dallaszkorben/diy-greenwall/3D/STL/lamp.hanger/lamp.hanger_console_extention.3mf

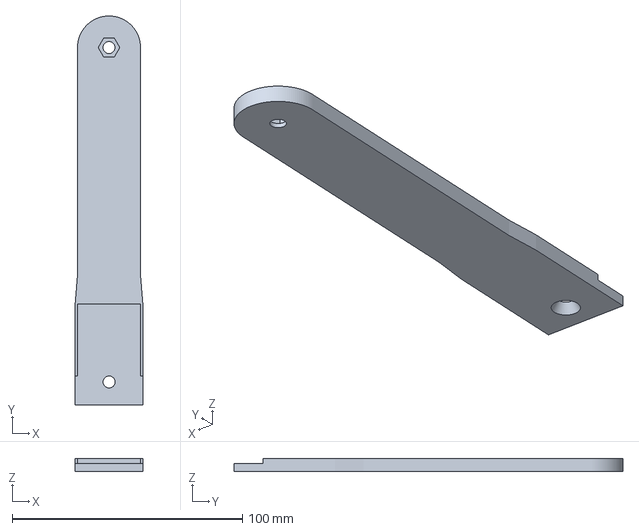
[picture p31: CAD file, 2024-04-21]
3D/STL/lamp.hanger/lamp.hanger_console_extention.3mf
29.4 x 169.0 x 5.50 mm
