dallaszkorben/diy-greenwall/3D/STL/pipe/spillway.reducer.FCStd

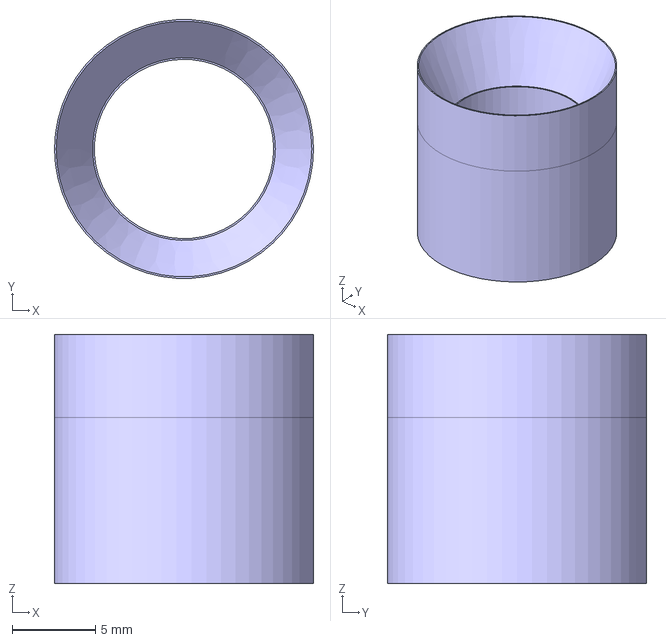
[picture p32: CAD file, 2022-04-12]
3D/STL/pipe/spillway.reducer.FCStd
15.6 x 15.6 x 15.0 mm
