dallaszkorben/diy-greenwall/3D/STL/round.container.hanger/Round.Container.Hanger.118mm.3mf

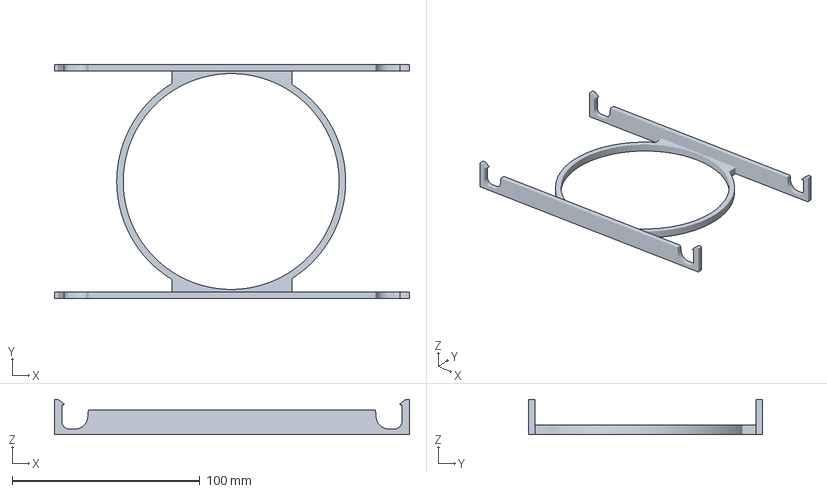
[picture p33: CAD file, 2024-04-21]
3D/STL/round.container.hanger/Round.Container.Hanger.118mm.3mf
189.2 x 124.9 x 18.7 mm
