dallaszkorben/diy-greenwall/3D/STL/sonic.sensor.cap.stl

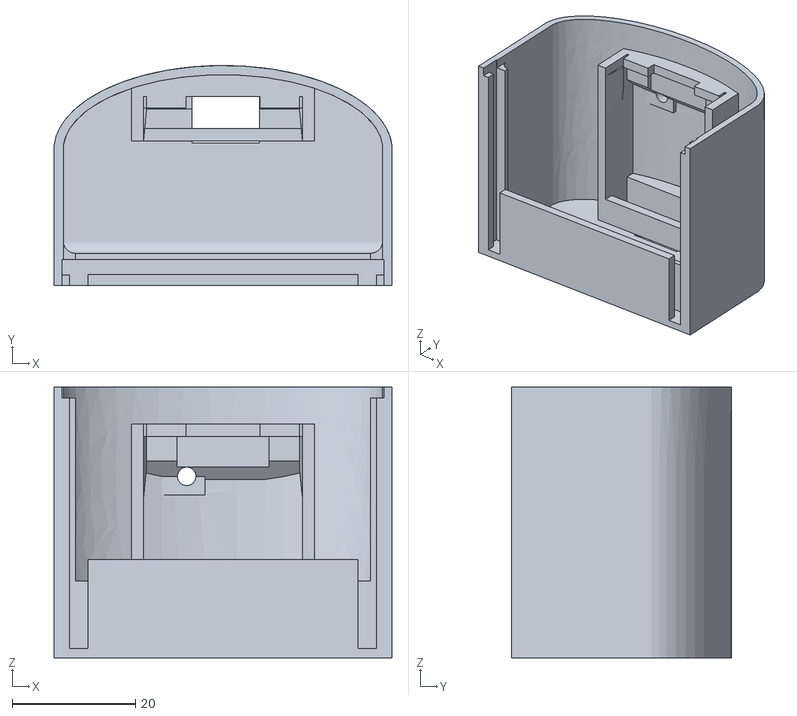
[picture p34: CAD file, 2021-12-05]
3D/STL/sonic.sensor.cap.stl
54.9 x 35.7 x 44.0
