dallaszkorben/diy-greenwall/3D/STL/station.lamp.pump/station.lamp.pump.100w.C8.stl

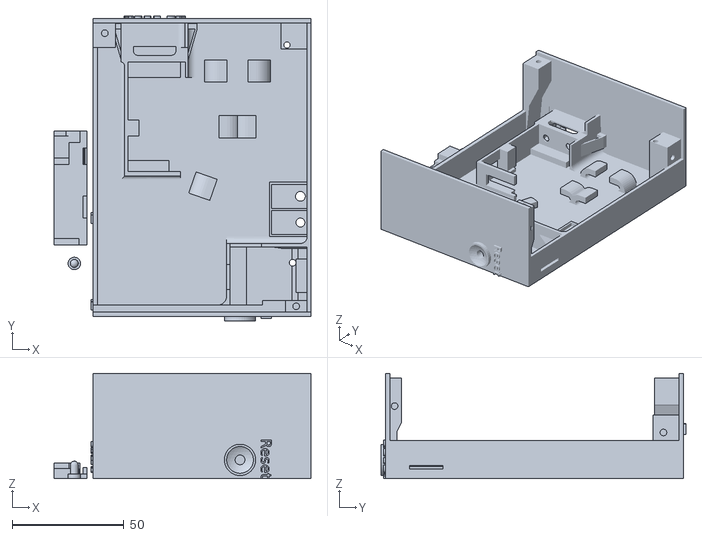
[picture p35: CAD file, 2022-08-27]
3D/STL/station.lamp.pump/station.lamp.pump.100w.C8.stl
114.9 x 136.2 x 47.0
