dallaszkorben/diy-greenwall/3D/STL/station.lamp/station.lamp.1X42v.stl

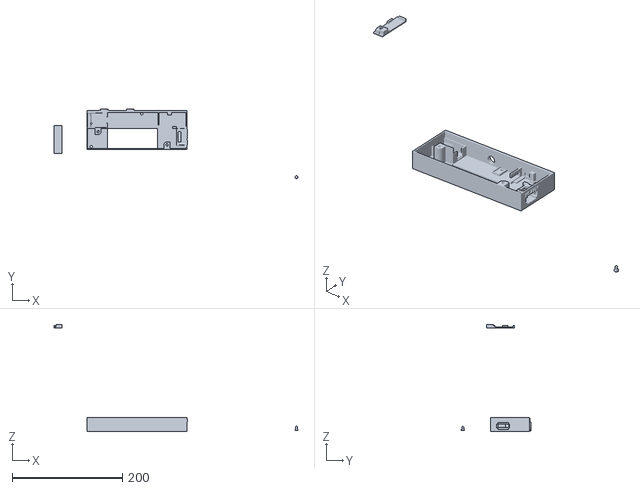
[picture p36: CAD file, 2024-08-11]
3D/STL/station.lamp/station.lamp.1X42v.stl
442.3 x 126.0 x 194.5
