dallaszkorben/diy-greenwall/3D/STL/station.pump/station.pump.1X12v-Frame.stl

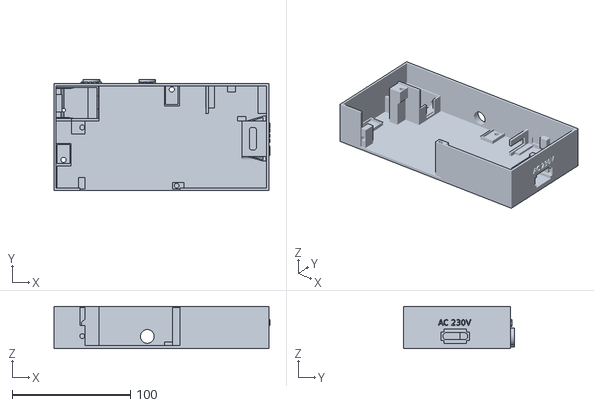
[picture p37: CAD file, 2024-08-11]
3D/STL/station.pump/station.pump.1X12v-Frame.stl
182.8 x 94.0 x 35.7
