dallaszkorben/diy-greenwall/3D/STL/station.sensor/station.sensor.console.stl

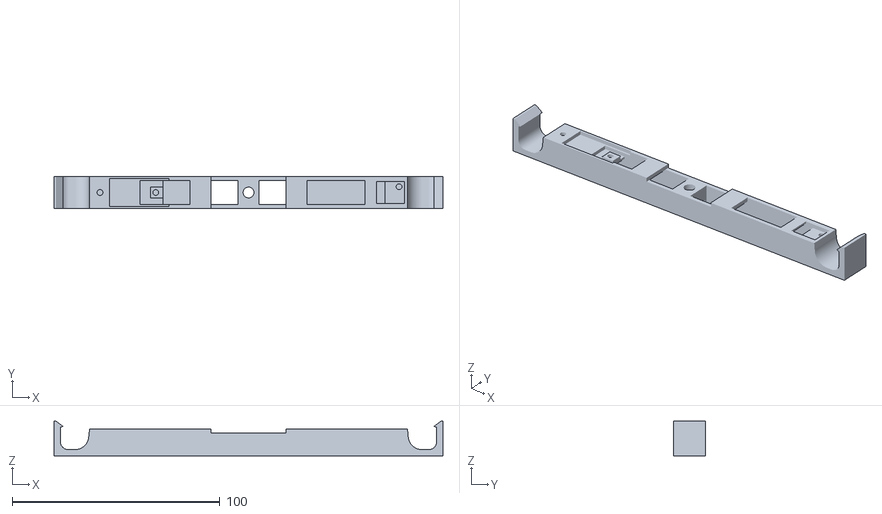
[picture p38: CAD file, 2022-10-24]
3D/STL/station.sensor/station.sensor.console.stl
187.2 x 15.6 x 16.7
