dallaszkorben/diy-greenwall/3D/STL/tmp/capacitor.FCStd

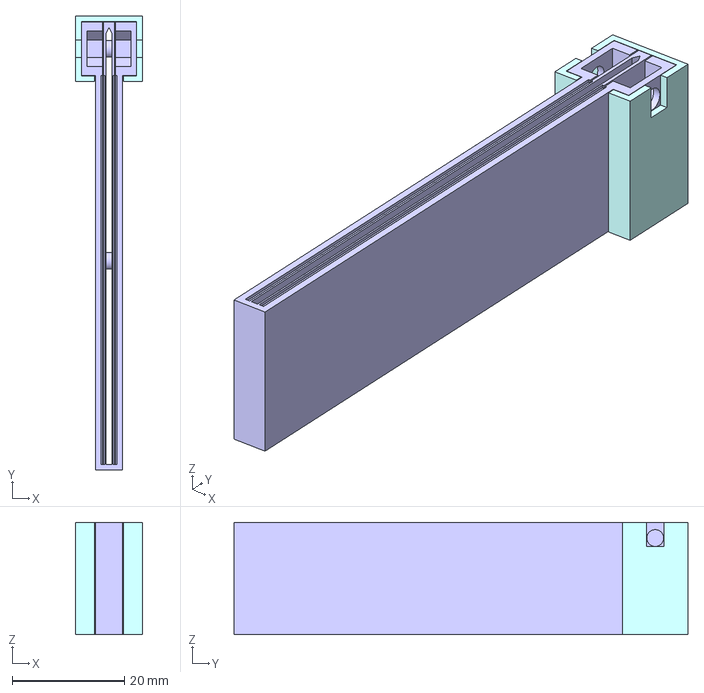
[picture p39: CAD file, 2023-01-22]
3D/STL/tmp/capacitor.FCStd
11.9 x 81.1 x 20.0 mm
