dallaszkorben/diy-greenwall/3D/STL/watertank/watertank_clamp.stl

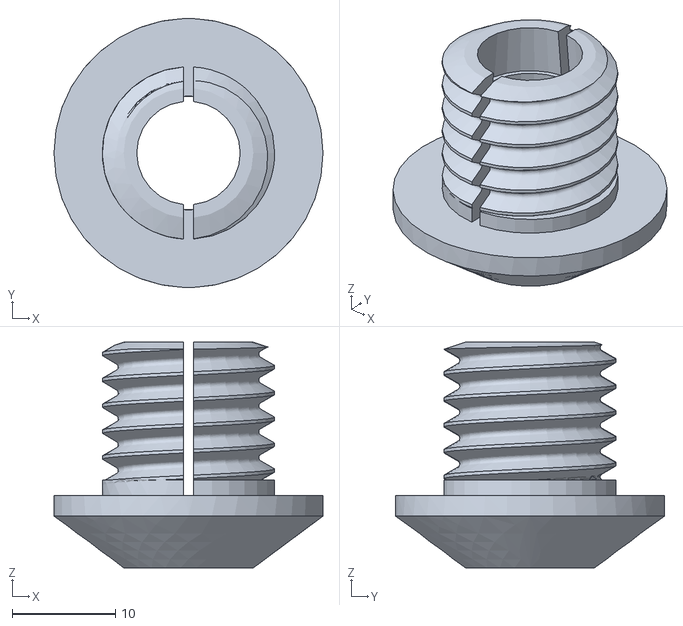
[picture p40: CAD file, 2022-04-16]
3D/STL/watertank/watertank_clamp.stl
26.0 x 26.0 x 21.8
