dallaszkorben/diy-greenwall/3D/FREECAD/camera/camera.wroover.FCStd

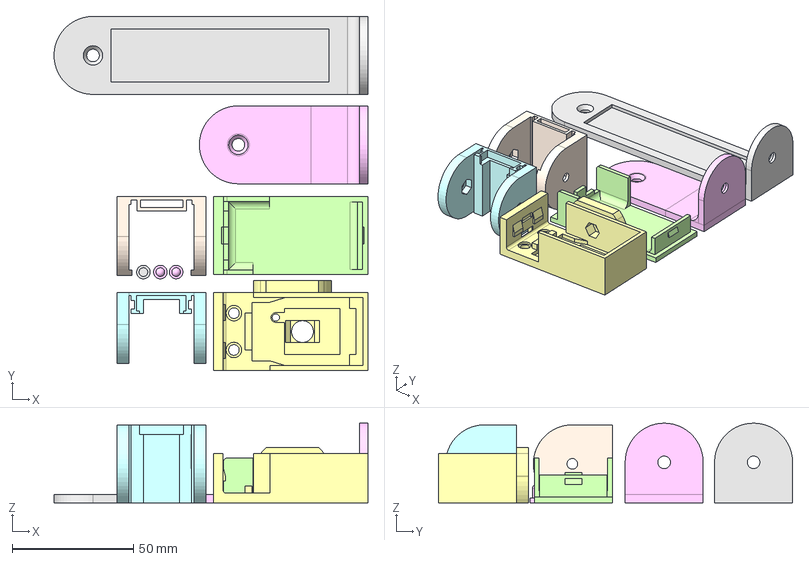
[picture p41: CAD file, 2022-10-02]
3D/FREECAD/camera/camera.wroover.FCStd
129.6 x 146.2 x 32.9 mm
Console
Rail-Reverse001
Rail-Straight
Button 2
Button 1
Button-cut
Frame
