dallaszkorben/diy-greenwall/3D/FREECAD/lamp/tmp2.FCStd

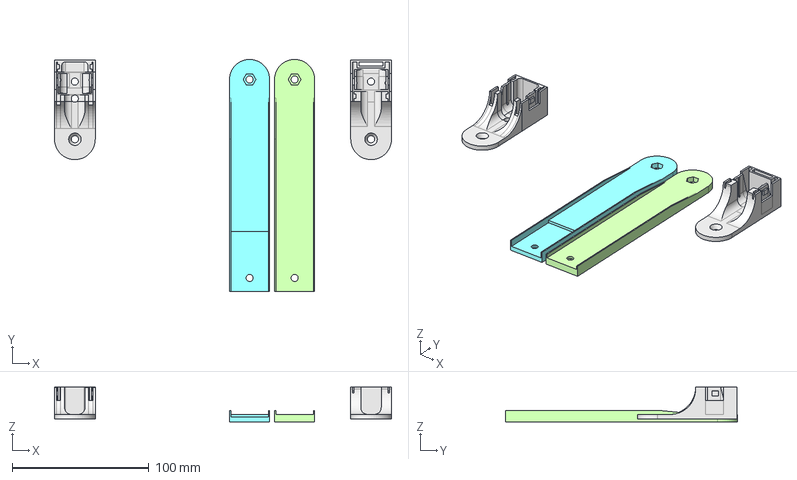
[picture p42: CAD file, 2022-08-27]
3D/FREECAD/lamp/tmp2.FCStd
246.8 x 170.0 x 25.5 mm
Slice.1
Slice002.1
Slice002.003
