dallaszkorben/diy-greenwall/3D/FREECAD/overflow/overflow.cap.FCStd

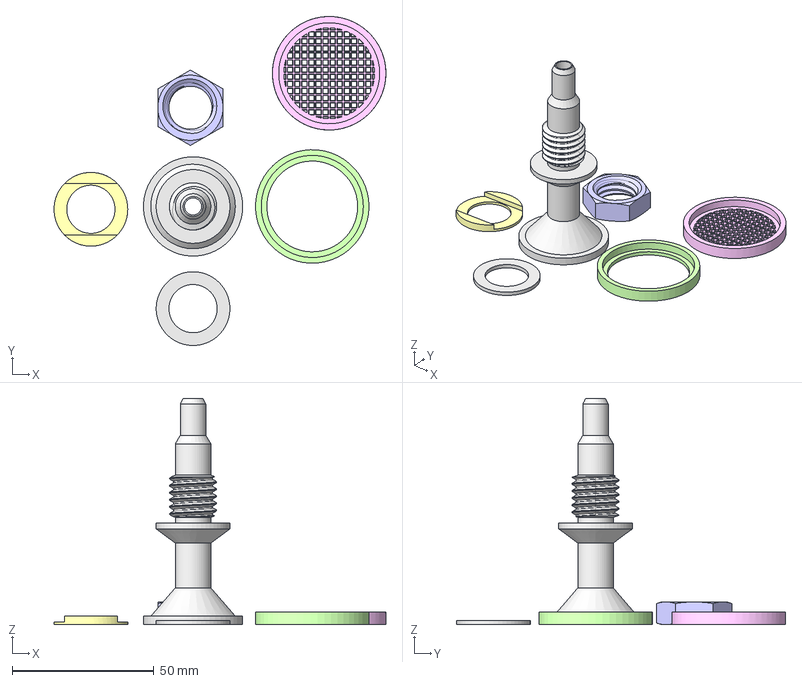
[picture p43: CAD file, 2022-05-15]
3D/FREECAD/overflow/overflow.cap.FCStd
116.9 x 115.9 x 79.7 mm
Pipe
Nut-R=9,003
