dallaszkorben/diy-greenwall/3D/FREECAD/station.lamp.pump/tmp2.FCStd

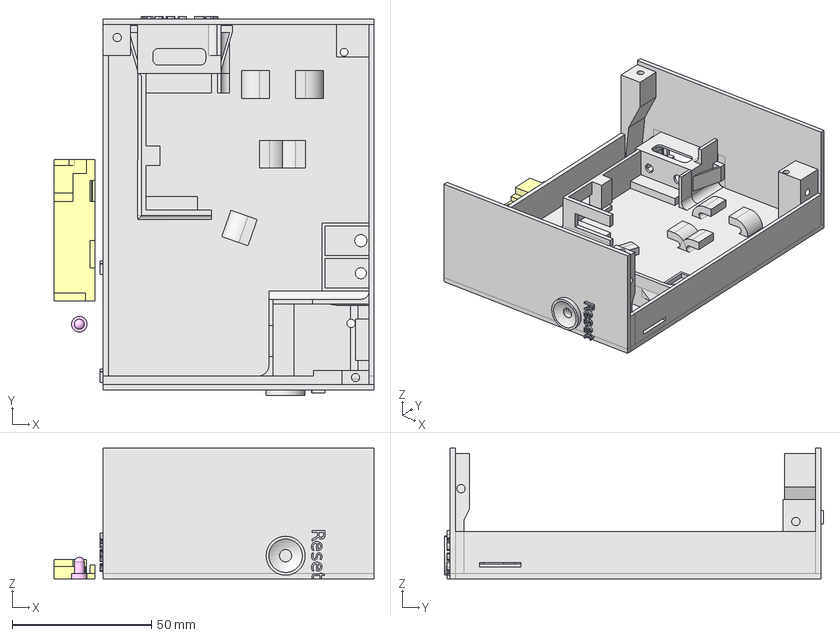
[picture p44: CAD file, 2022-08-27]
3D/FREECAD/station.lamp.pump/tmp2.FCStd
114.9 x 136.2 x 47.0 mm
Pump
Module
AC230V
Lamp
MOSFET001
Power.Supply
Connector.2
