dallaszkorben/diy-greenwall/3D/FREECAD/tmp.FCStd

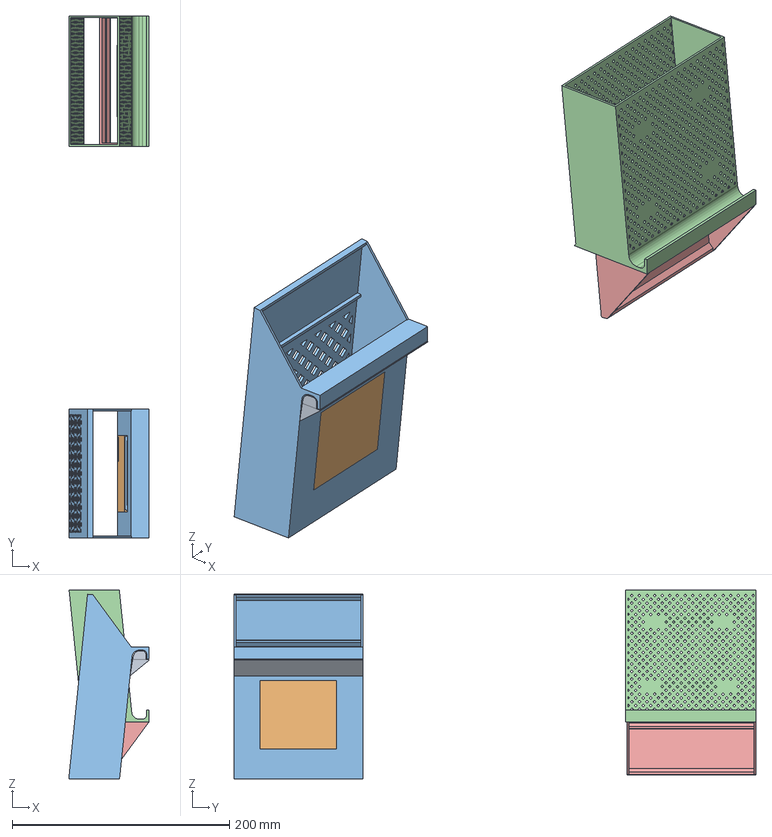
[picture p45: CAD file, 2022-08-14]
3D/FREECAD/tmp.FCStd
74.1 x 480.8 x 173.8 mm
Slice001.0
Slice.002
