dallaszkorben/diy-greenwall/3D/STL/camera/camera.wroover.nested_console.middle.stl

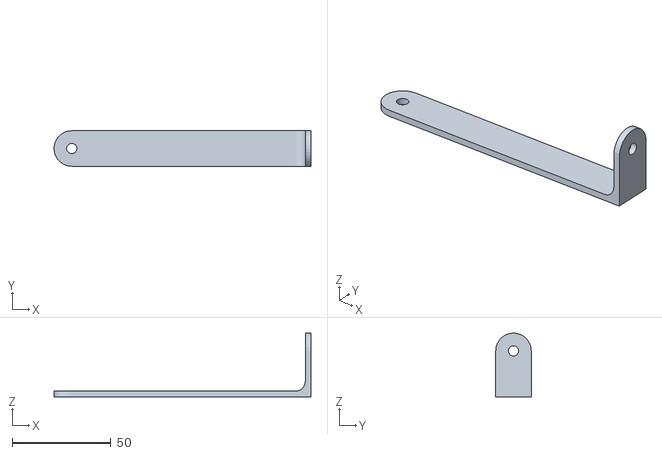
[picture p46: CAD file, 2022-10-02]
3D/STL/camera/camera.wroover.nested_console.middle.stl
130.0 x 18.0 x 32.3
