dallaszkorben/diy-greenwall/3D/STL/container/container-bottom.V4.stl

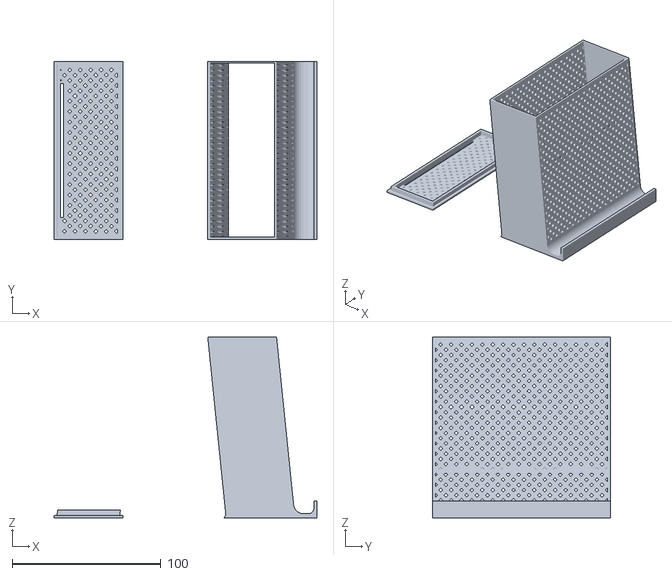
[picture p47: CAD file, 2021-09-12]
3D/STL/container/container-bottom.V4.stl
176.9 x 120.0 x 121.6
