dallaszkorben/diy-greenwall/3D/STL/controlbox/controlbox-button.stl

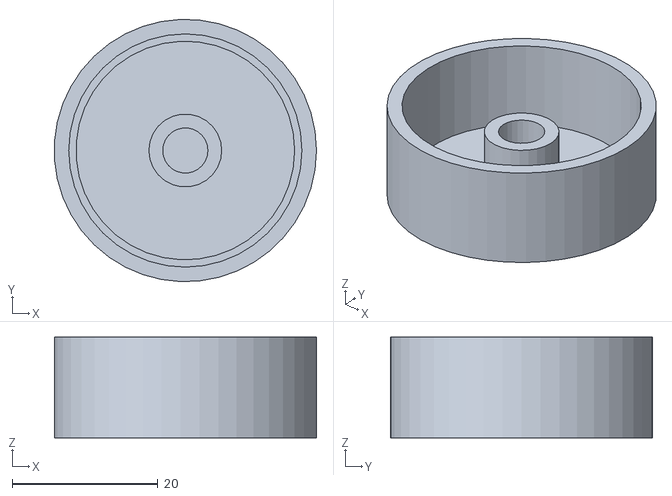
[picture p48: CAD file, 2022-01-23]
3D/STL/controlbox/controlbox-button.stl
36.0 x 36.0 x 13.8
