dallaszkorben/diy-greenwall/3D/STL/lamp.hanger/lamp.hanger_cap_straight_open.stl

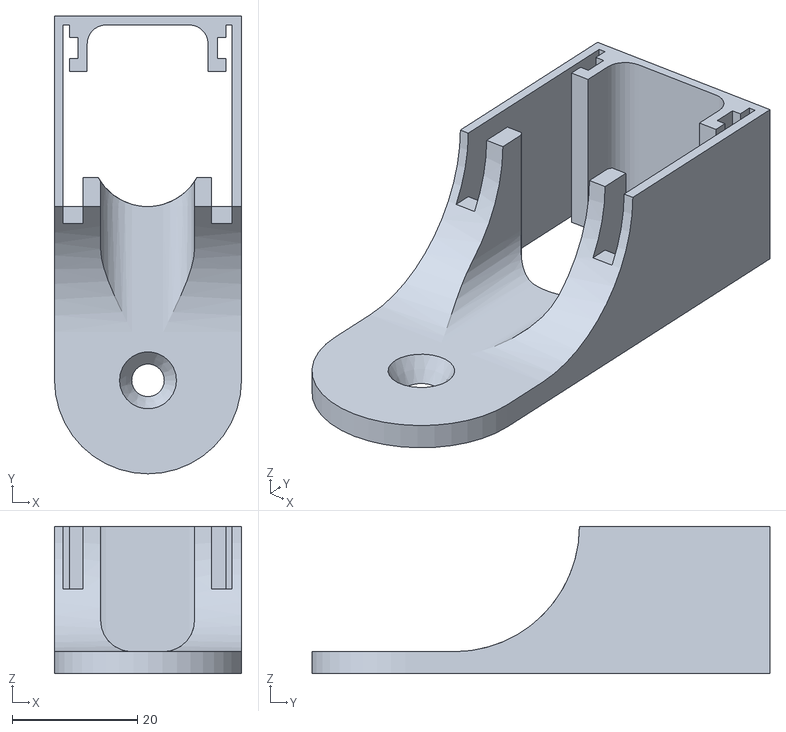
[picture p49: CAD file, 2022-09-19]
3D/STL/lamp.hanger/lamp.hanger_cap_straight_open.stl
29.9 x 73.1 x 23.5
