dallaszkorben/diy-greenwall/3D/STL/owerflow/overflow_with_filter.amf

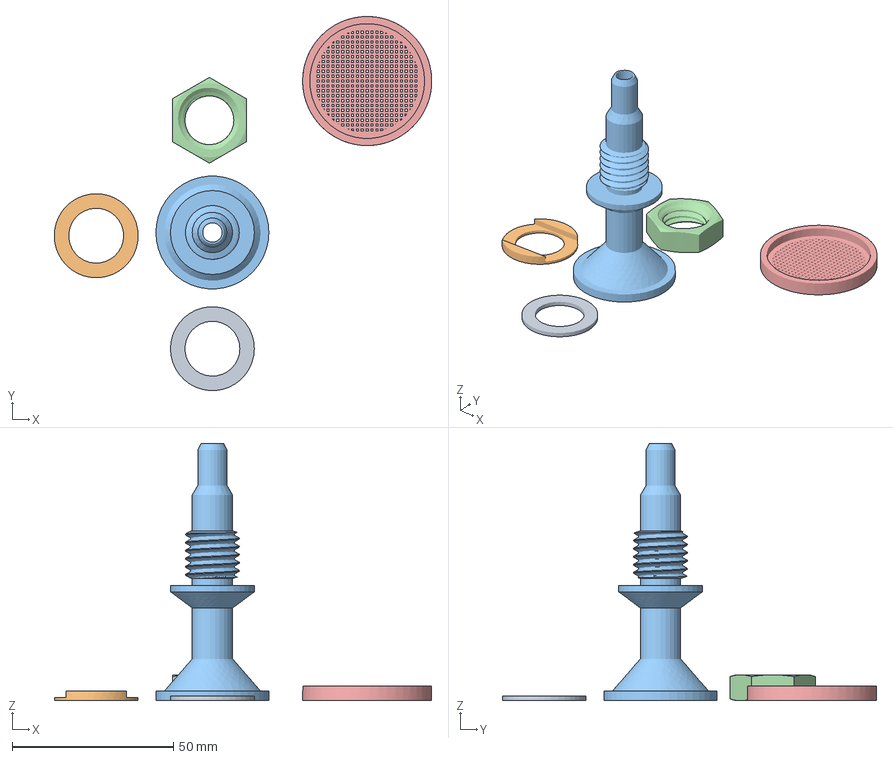
[picture p50: CAD file, 2022-05-15]
3D/STL/owerflow/overflow_with_filter.amf
117.0 x 115.9 x 79.7 mm
Pipe
Nut-R=9,003
