dallaszkorben/diy-greenwall/3D/STL/pipe/spillway.extender.FCStd

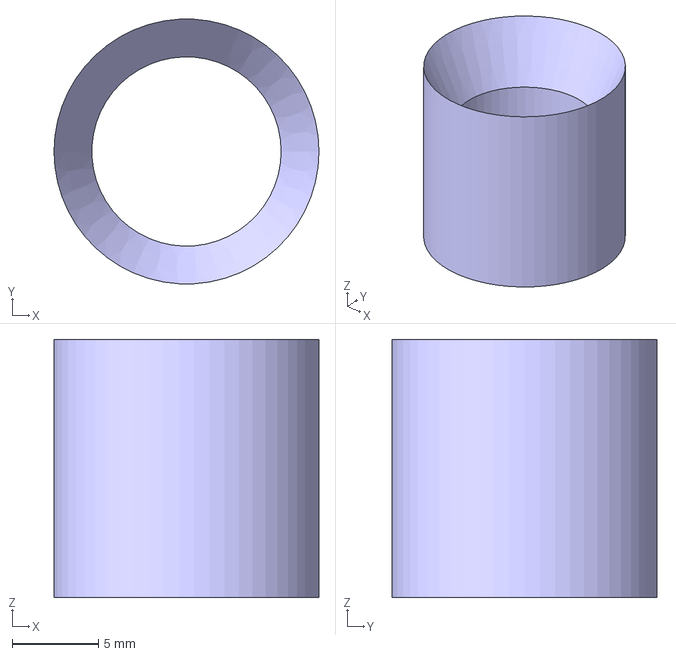
[picture p51: CAD file, 2022-04-12]
3D/STL/pipe/spillway.extender.FCStd
15.4 x 15.4 x 15.0 mm
