dallaszkorben/diy-greenwall/3D/STL/sonic.sensor.frame.stl

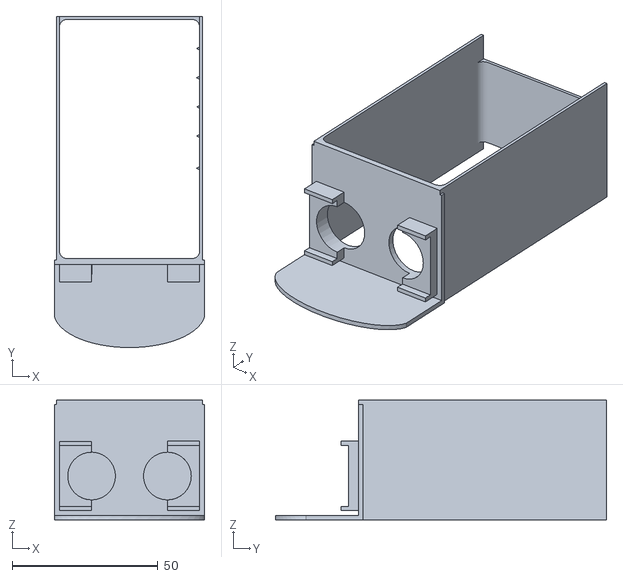
[picture p53: CAD file, 2021-12-05]
3D/STL/sonic.sensor.frame.stl
51.5 x 113.5 x 41.0
