dallaszkorben/diy-greenwall/3D/STL/station.lamp.pump/station.lamp.pump.50w.stl

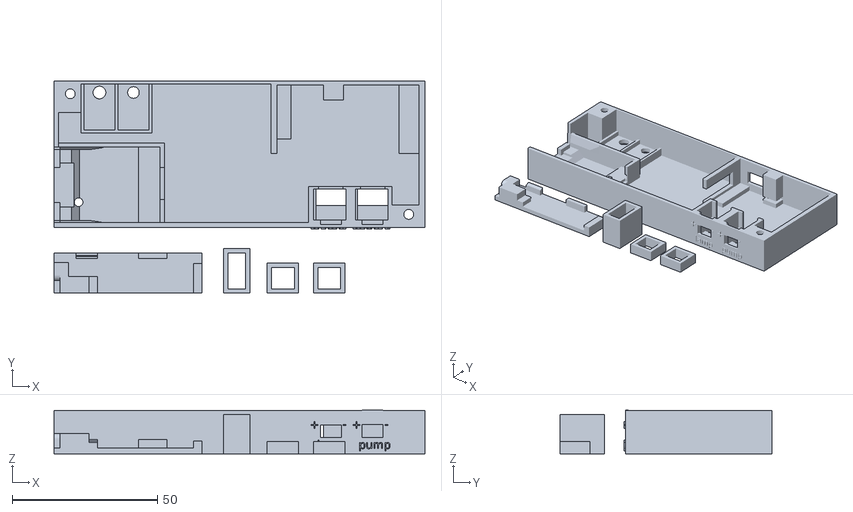
[picture p54: CAD file, 2022-04-12]
3D/STL/station.lamp.pump/station.lamp.pump.50w.stl
127.7 x 73.1 x 15.1
