dallaszkorben/diy-greenwall/3D/STL/station.lamp/station.lamp.1X42v-Separator.stl

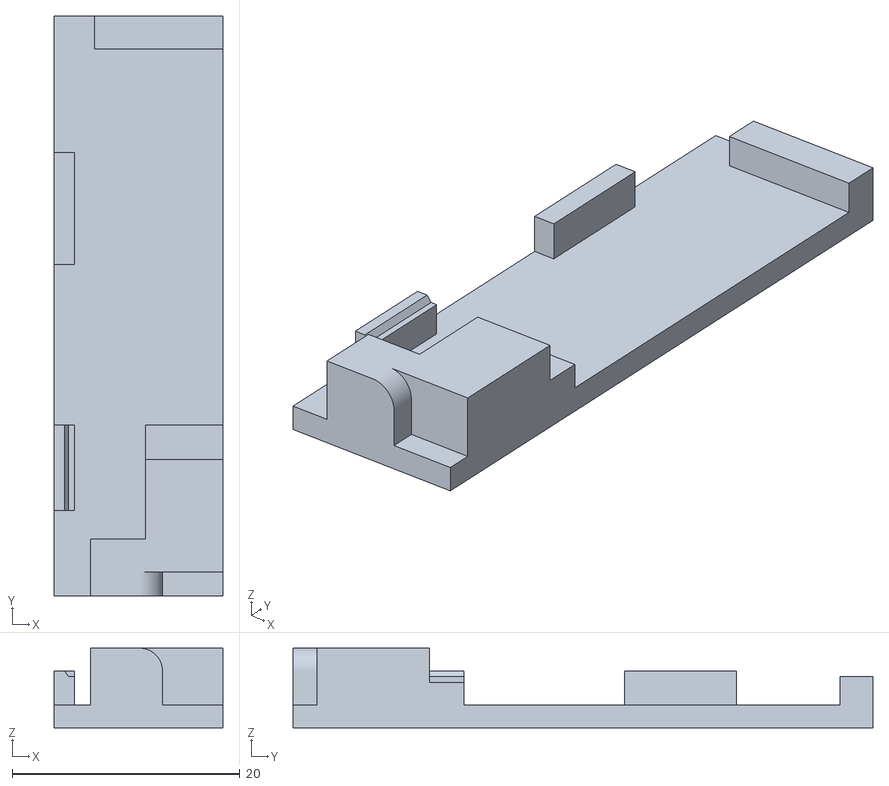
[picture p55: CAD file, 2024-08-11]
3D/STL/station.lamp/station.lamp.1X42v-Separator.stl
14.8 x 50.9 x 7.00
