dallaszkorben/diy-greenwall/3D/STL/tmp/station.sensor-capacitor.stl

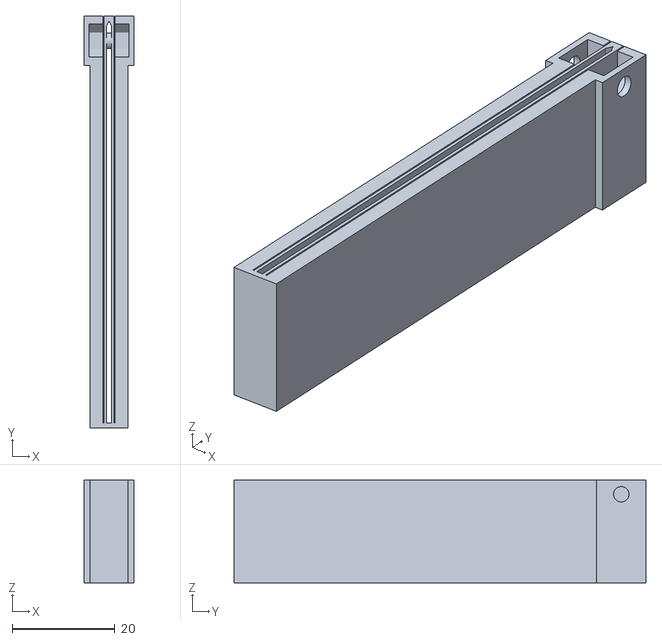
[picture p56: CAD file, 2023-01-22]
3D/STL/tmp/station.sensor-capacitor.stl
9.80 x 80.0 x 20.0
