dallaszkorben/diy-greenwall/3D/FREECAD/camera/camera.new.FCStd

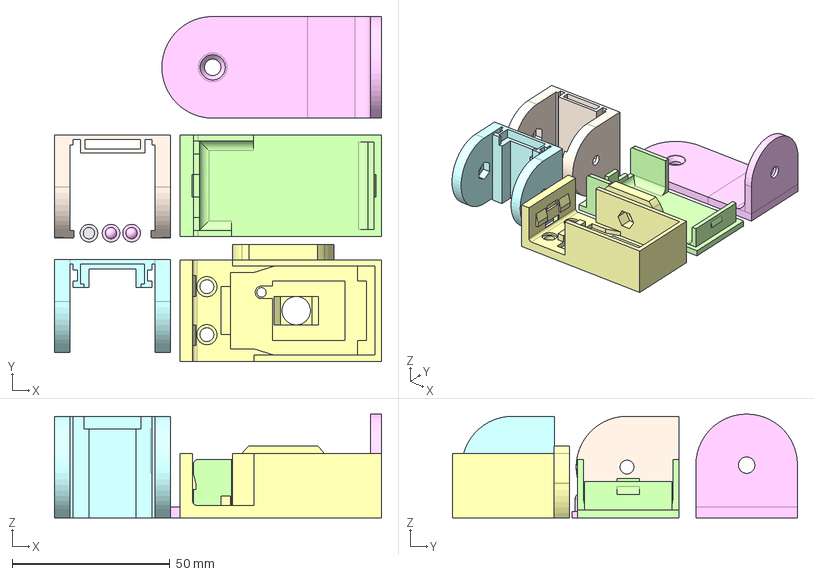
[picture p57: CAD file, 2022-09-24]
3D/FREECAD/camera/camera.new.FCStd
103.6 x 109.3 x 32.9 mm
Console
Rail-Reverse001
Rail-Straight
Frame003
Frame
Button 2
Button 1
Button-cut
