dallaszkorben/diy-greenwall/3D/FREECAD/lamp/tmp.FCStd

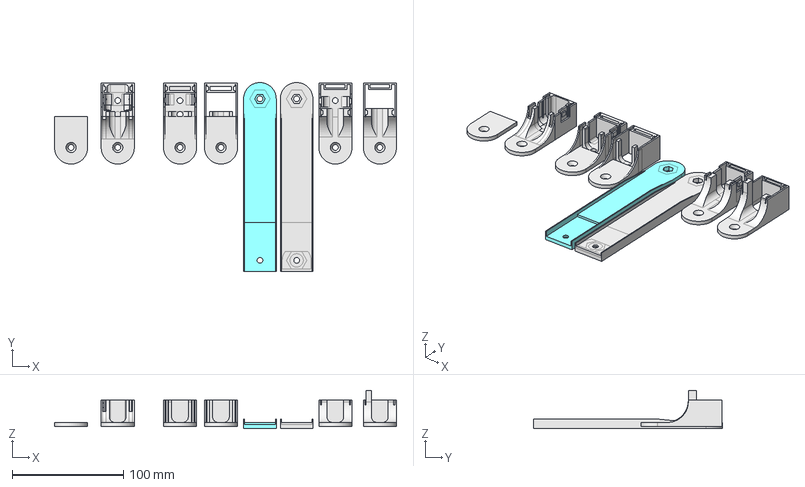
[picture p58: CAD file, 2022-08-27]
3D/FREECAD/lamp/tmp.FCStd
307.8 x 170.0 x 34.2 mm
Slice007.2
Slice008.1
Slice009.0
Slice009.1
Slice003.004
