dallaszkorben/diy-greenwall/3D/FREECAD/overflow-8.6_9.2.FCStd

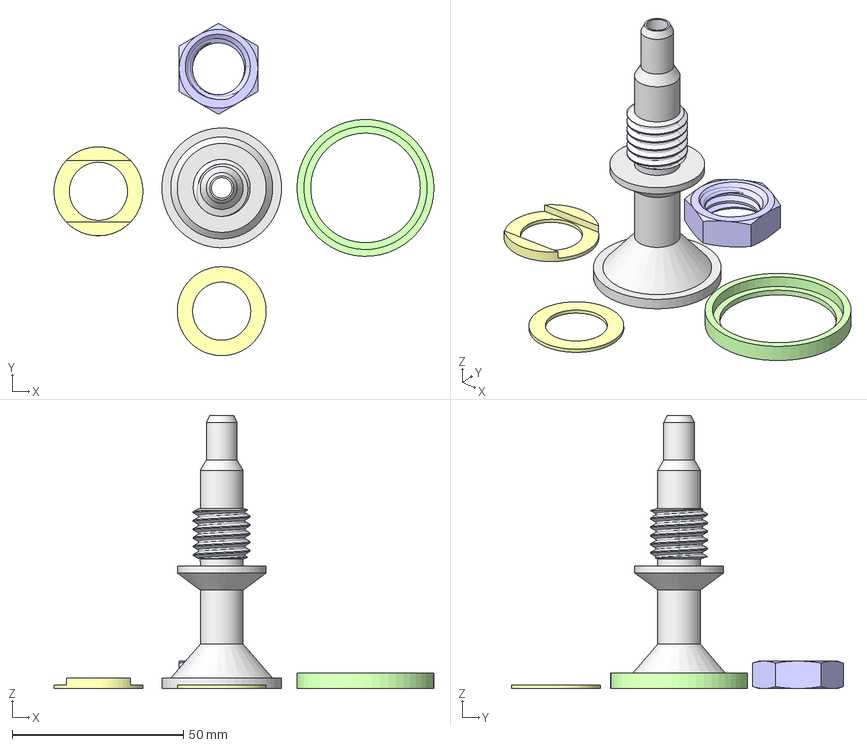
[picture p59: CAD file, 2022-04-15]
3D/FREECAD/overflow-8.6_9.2.FCStd
111.0 x 97.0 x 79.7 mm
Pipe
Nut-R=9,003
