dallaszkorben/diy-greenwall/3D/FREECAD/station.lamp.pump/tmp3.FCStd

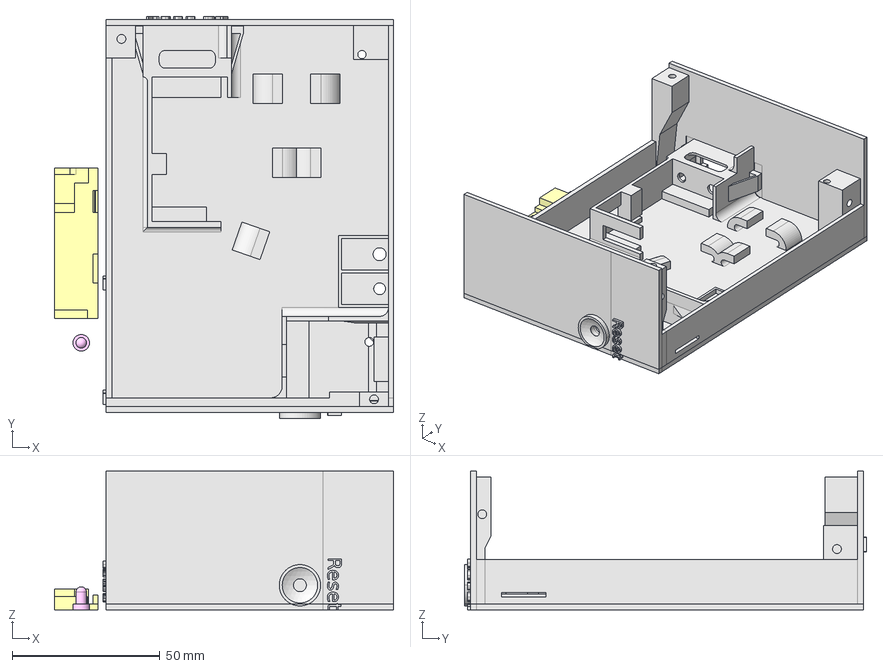
[picture p60: CAD file, 2022-08-27]
3D/FREECAD/station.lamp.pump/tmp3.FCStd
114.9 x 136.2 x 47.0 mm
Slice.0
Slice.2
Text001
Frame
