dallaszkorben/diy-greenwall/3D/STL/camera/camera.wrover.nested_frame.stl

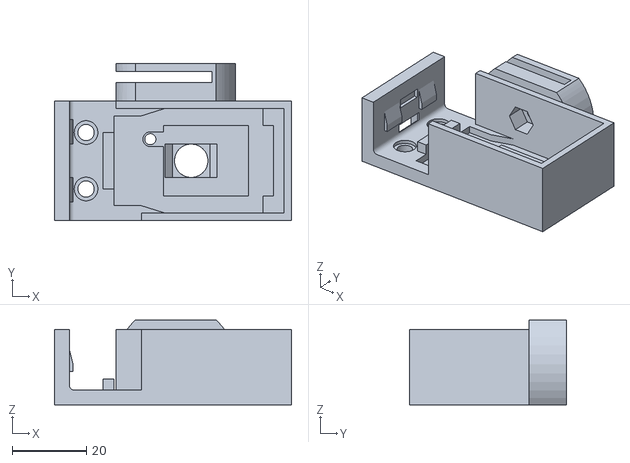
[picture p61: CAD file, 2022-10-02]
3D/STL/camera/camera.wrover.nested_frame.stl
63.8 x 42.3 x 22.8
