dallaszkorben/diy-greenwall/3D/STL/controlbox/controlbox-front-panel.stl

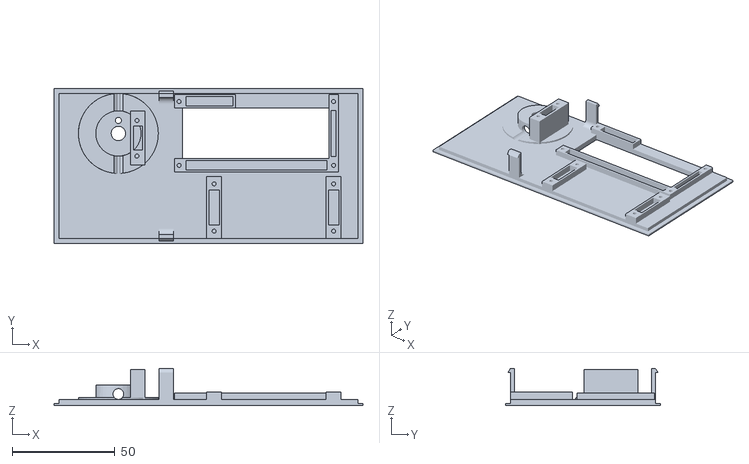
[picture p62: CAD file, 2022-01-23]
3D/STL/controlbox/controlbox-front-panel.stl
150.0 x 75.1 x 18.0
