dallaszkorben/diy-greenwall/3D/STL/pipe/pipe.clamp-curve.1.part.stl

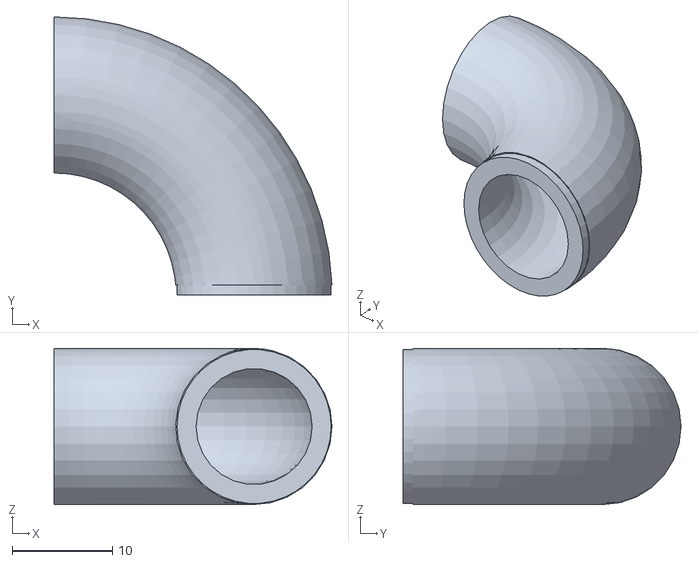
[picture p65: CAD file, 2021-09-19]
3D/STL/pipe/pipe.clamp-curve.1.part.stl
27.8 x 27.8 x 15.6
