dallaszkorben/diy-greenwall/3D/STL/sonic.sensor.all.stl

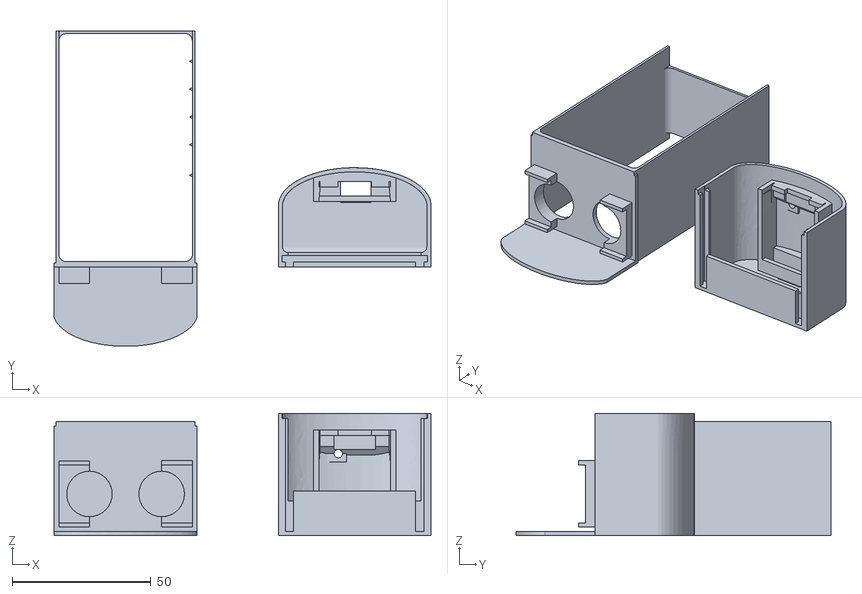
[picture p66: CAD file, 2021-12-05]
3D/STL/sonic.sensor.all.stl
135.7 x 113.5 x 44.0
