dallaszkorben/diy-greenwall/3D/STL/station.lamp/station.lamp.1X42v-Button.stl

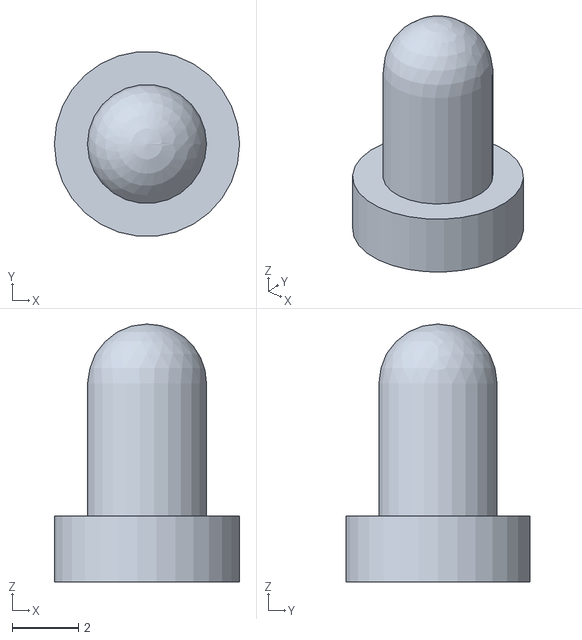
[picture p67: CAD file, 2024-08-11]
3D/STL/station.lamp/station.lamp.1X42v-Button.stl
5.60 x 5.57 x 7.80
