dallaszkorben/diy-greenwall/3D/STL/station.sensor/station.sensor.sonar.cap.stl

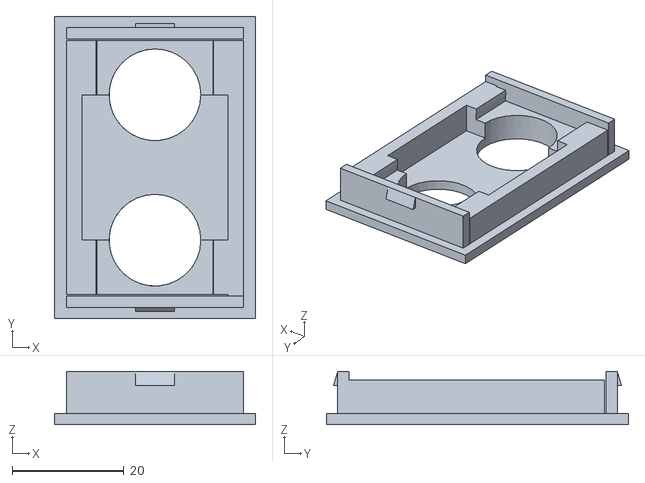
[picture p68: CAD file, 2022-10-15]
3D/STL/station.sensor/station.sensor.sonar.cap.stl
35.9 x 54.0 x 9.50
