dallaszkorben/diy-greenwall/3D/STL/tmp/station.sensor-capacitor.cap.stl

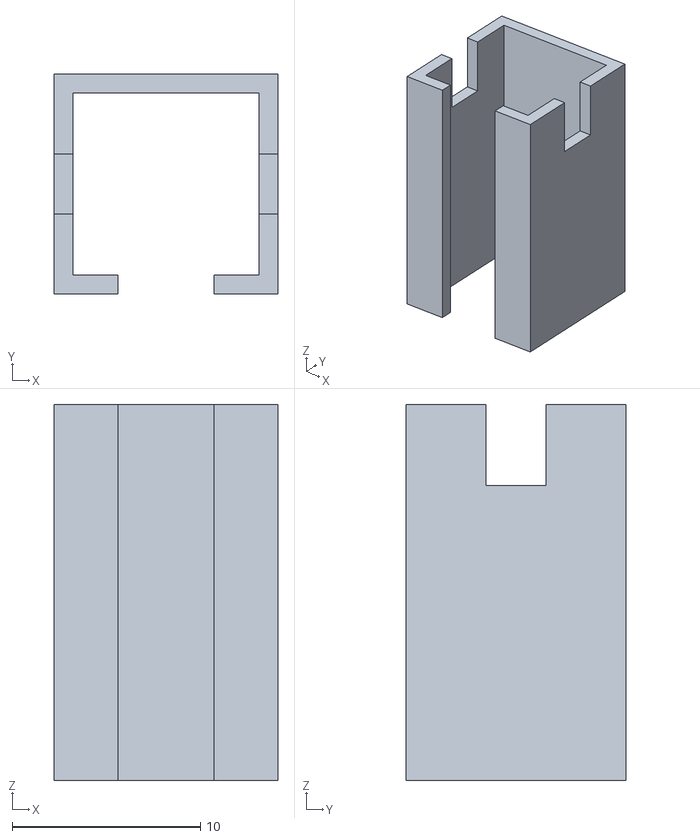
[picture p69: CAD file, 2023-01-22]
3D/STL/tmp/station.sensor-capacitor.cap.stl
11.9 x 11.7 x 20.0
