dallaszkorben/diy-greenwall/3D/FREECAD/camera/camera.FCStd

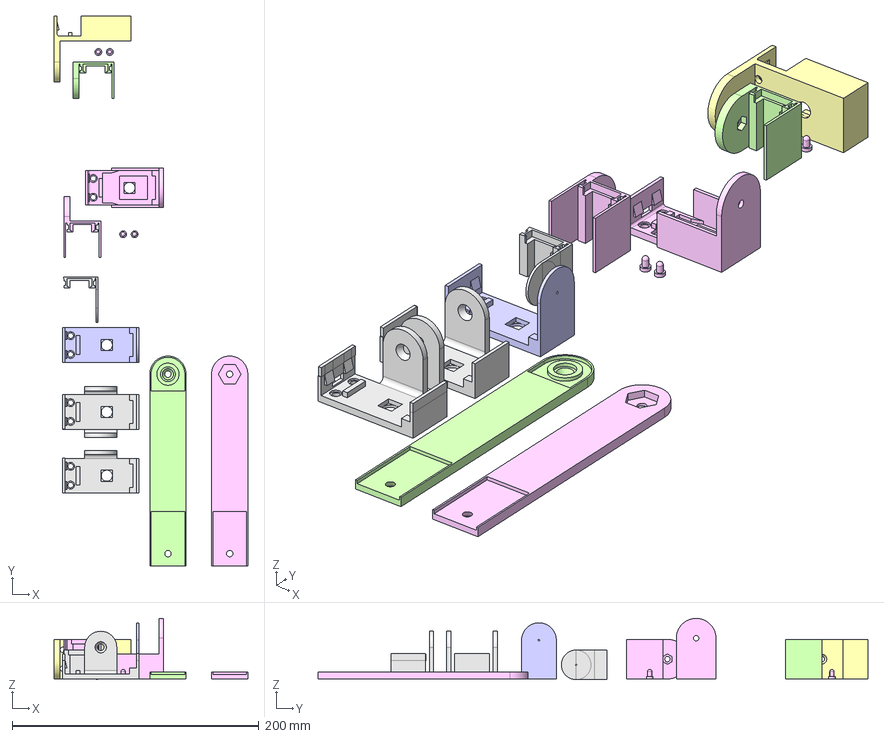
[picture p70: CAD file, 2022-05-26]
3D/FREECAD/camera/camera.FCStd
156.9 x 445.4 x 49.6 mm
Slice008.1
Slice008.2
Slice008.003
