dallaszkorben/diy-greenwall/3D/FREECAD/cone.FCStd

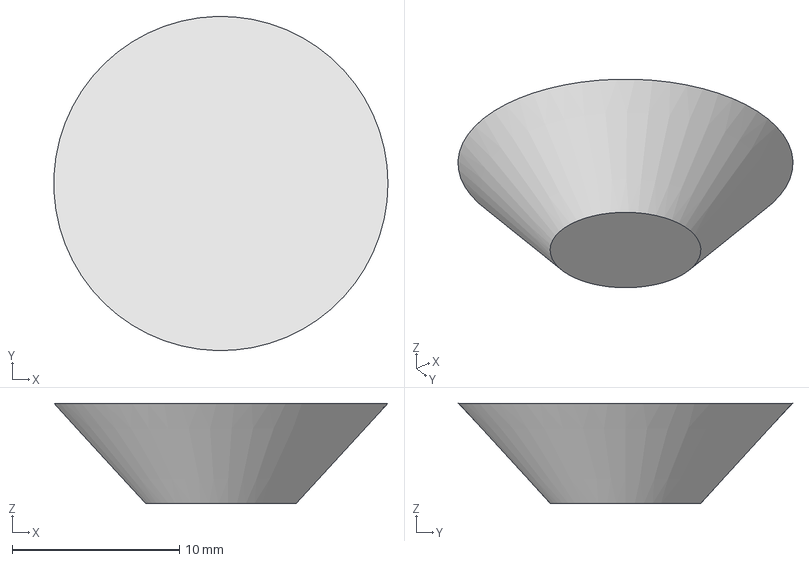
[picture p71: CAD file, 2022-04-12]
3D/FREECAD/cone.FCStd
20.0 x 20.0 x 6.00 mm
