dallaszkorben/diy-greenwall/3D/FREECAD/lamp/lamp.hanger.new.FCStd

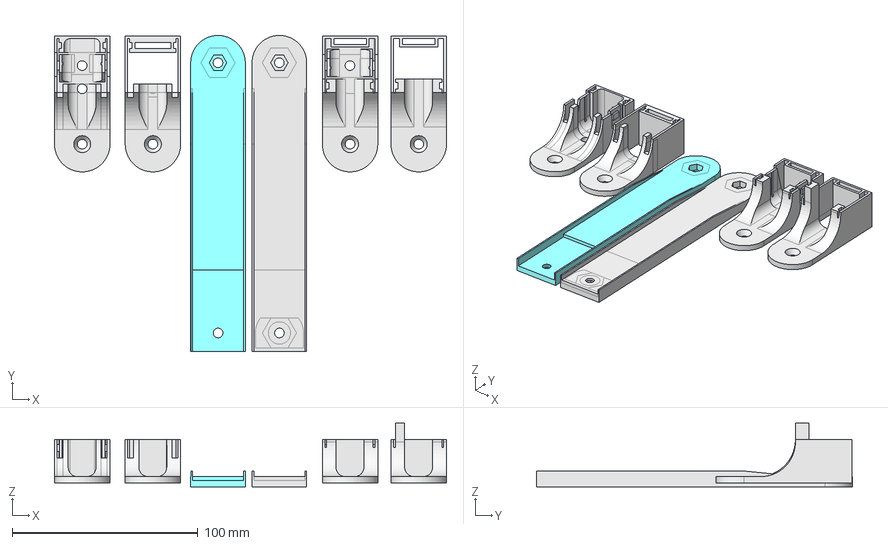
[picture p72: CAD file, 2022-08-27]
3D/FREECAD/lamp/lamp.hanger.new.FCStd
210.9 x 170.0 x 34.2 mm
