dallaszkorben/diy-greenwall/3D/FREECAD/overflow/overflow-8.8_9.2.FCStd

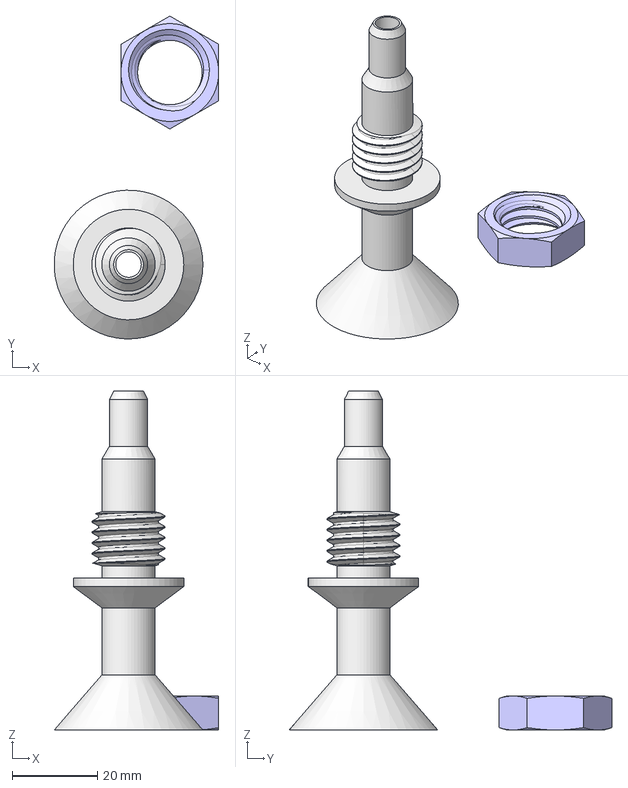
[picture p73: CAD file, 2022-04-16]
3D/FREECAD/overflow/overflow-8.8_9.2.FCStd
38.7 x 75.9 x 79.7 mm
Nut-R=9,2
