dallaszkorben/diy-greenwall/3D/FREECAD/station.lamp.pump/station.lamp.pump.100W.save.FCStd

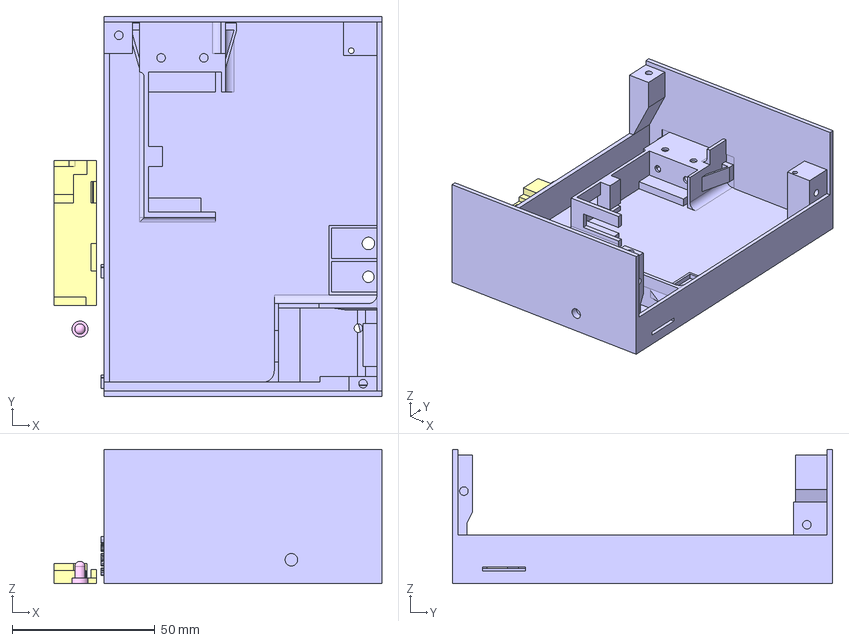
[picture p74: CAD file, 2022-08-27]
3D/FREECAD/station.lamp.pump/station.lamp.pump.100W.save.FCStd
114.9 x 133.2 x 47.0 mm
