dallaszkorben/diy-greenwall/3D/STL/camera/camera.wroover.nested_console.short.stl

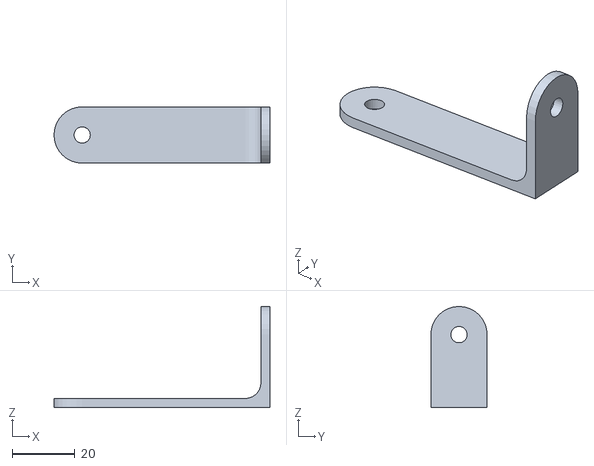
[picture p75: CAD file, 2022-10-02]
3D/STL/camera/camera.wroover.nested_console.short.stl
69.0 x 18.0 x 32.3
