dallaszkorben/diy-greenwall/3D/STL/controlbox/controlbox-back.stl

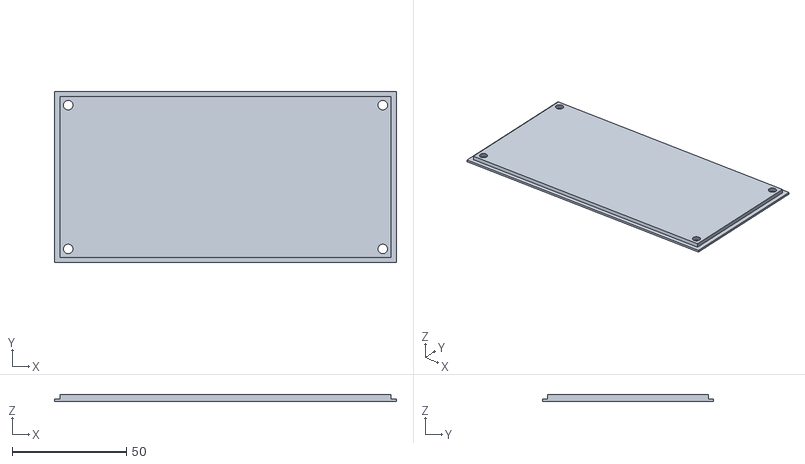
[picture p76: CAD file, 2022-01-23]
3D/STL/controlbox/controlbox-back.stl
150.0 x 75.1 x 3.00
