dallaszkorben/diy-greenwall/3D/STL/owerflow/overflow_ring_filter.amf

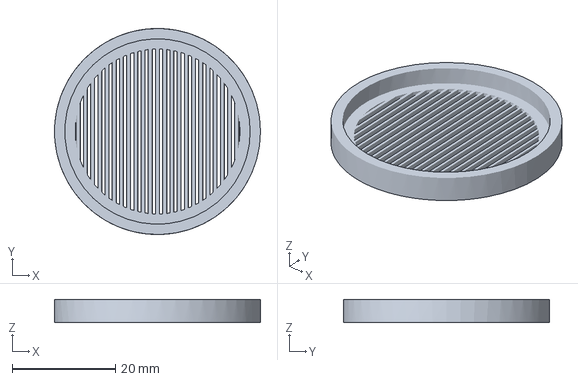
[picture p77: CAD file, 2022-05-15]
3D/STL/owerflow/overflow_ring_filter.amf
40.0 x 40.0 x 4.50 mm
