dallaszkorben/diy-greenwall/3D/STL/pipe/pipe.clamp-curve.2.parts.stl

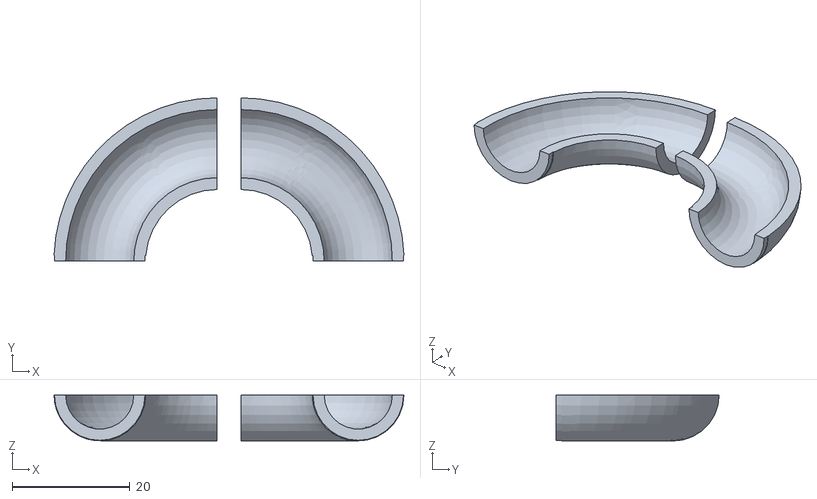
[picture p78: CAD file, 2021-09-19]
3D/STL/pipe/pipe.clamp-curve.2.parts.stl
59.6 x 27.8 x 7.80
