dallaszkorben/diy-greenwall/3D/STL/station.lamp/station.lamp.1X42v-Frame.stl

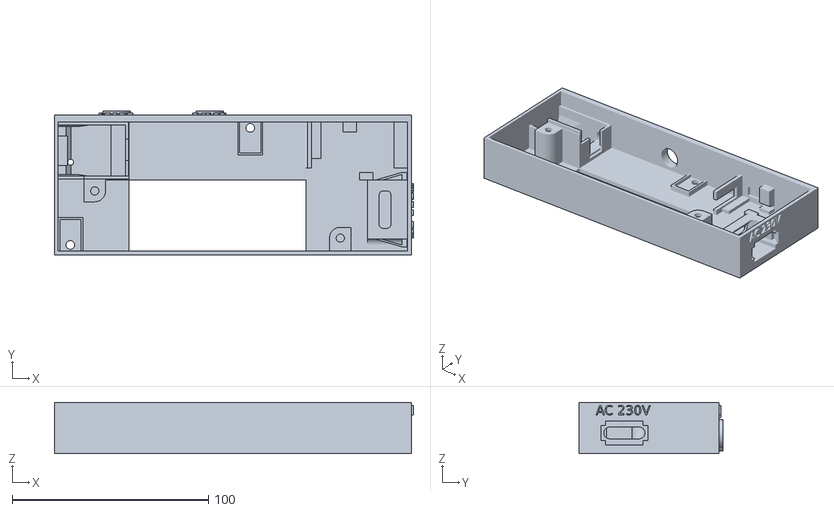
[picture p79: CAD file, 2024-08-11]
3D/STL/station.lamp/station.lamp.1X42v-Frame.stl
182.8 x 73.1 x 26.0
