dallaszkorben/diy-greenwall/3D/STL/station.sensor/station.sensor.box.stl

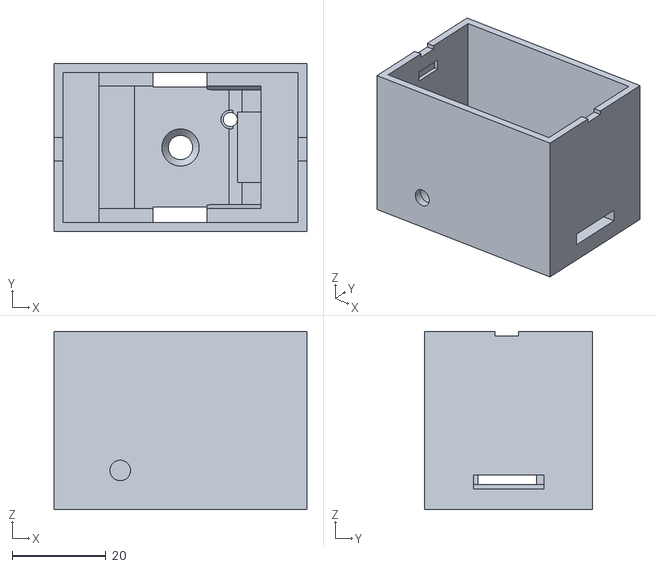
[picture p80: CAD file, 2022-10-15]
3D/STL/station.sensor/station.sensor.box.stl
54.0 x 35.9 x 38.0
