dallaszkorben/diy-greenwall/3D/FREECAD/a.FCStd

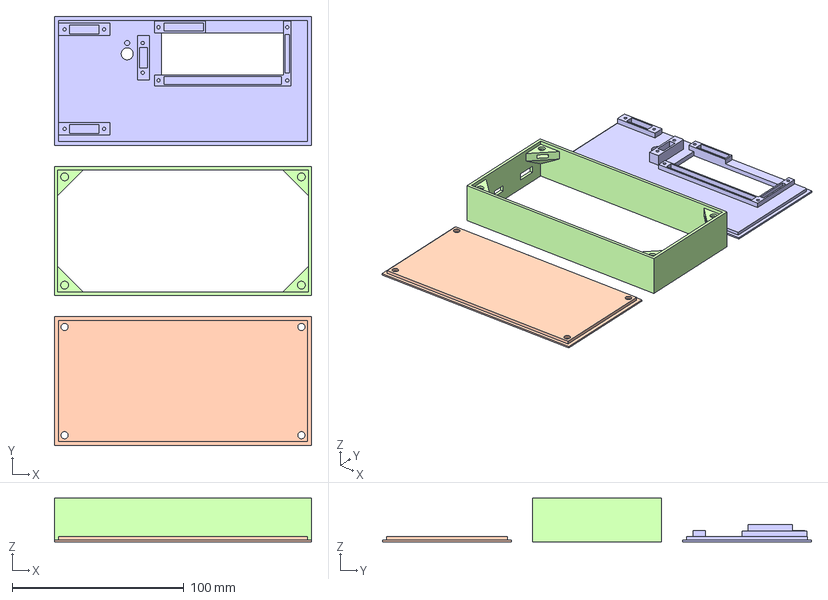
[picture p81: CAD file, 2022-01-23]
3D/FREECAD/a.FCStd
150.0 x 250.0 x 25.5 mm
