dallaszkorben/diy-greenwall/3D/FREECAD/station.lamp.pump/tmp.FCStd

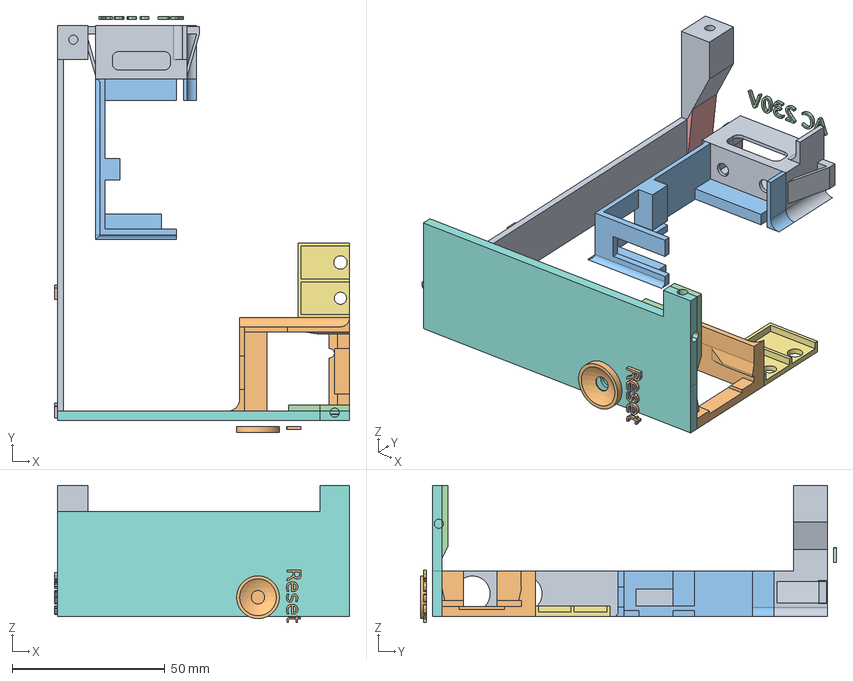
[picture p82: CAD file, 2022-08-27]
3D/FREECAD/station.lamp.pump/tmp.FCStd
96.7 x 136.2 x 45.0 mm
Connector.2
Reset.2
Power.Supply
AC230V
Lamp
Pump
Slice003.023
Slice004.006
Slice004.007
Slice004.008
Slice004.3
Slice004.4
