dallaszkorben/diy-greenwall/3D/STL/camera/camera.wroover.console.long.stl

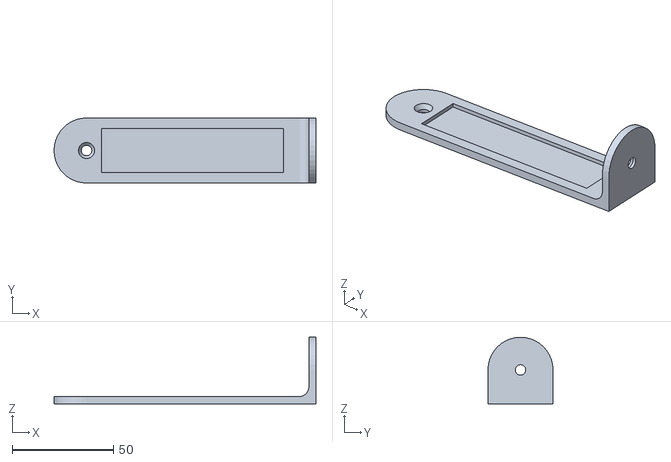
[picture p83: CAD file, 2022-10-02]
3D/STL/camera/camera.wroover.console.long.stl
129.6 x 32.2 x 32.9
