dallaszkorben/diy-greenwall/3D/STL/container/container.stl

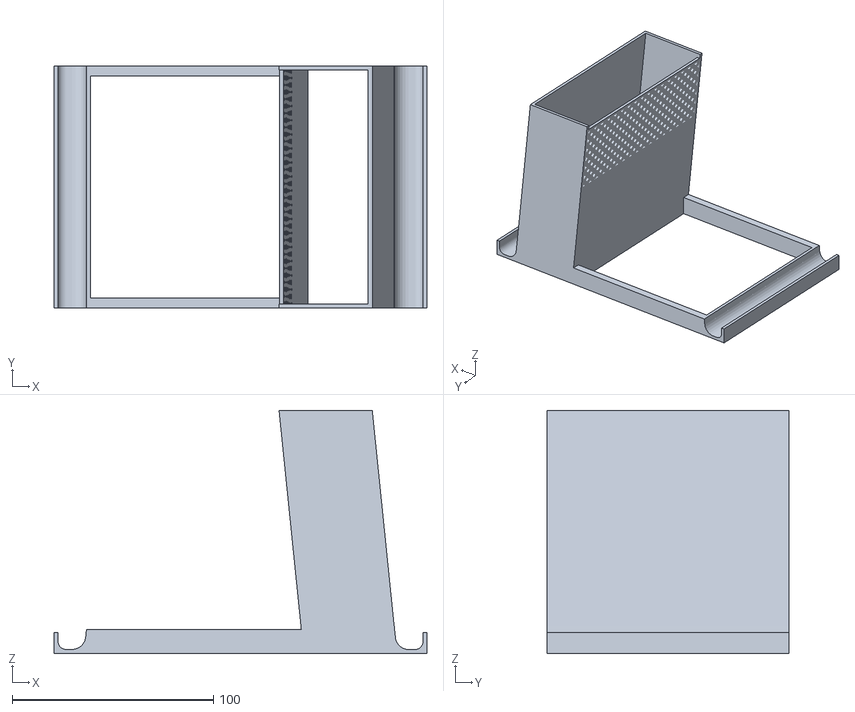
[picture p84: CAD file, 2021-09-12]
3D/STL/container/container.stl
185.2 x 120.0 x 120.8
