dallaszkorben/diy-greenwall/3D/STL/controlbox/controlbox-button-with-hole.stl

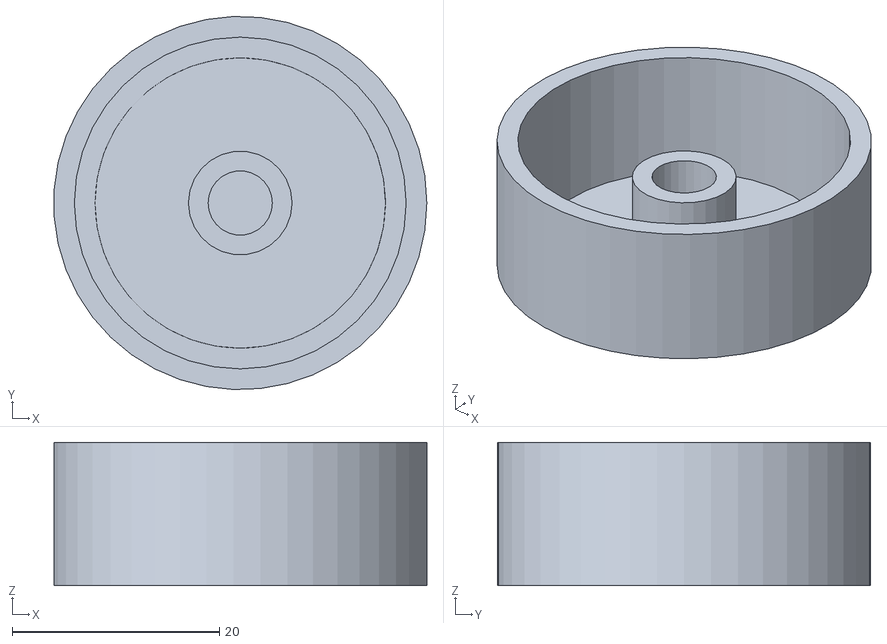
[picture p85: CAD file, 2022-01-23]
3D/STL/controlbox/controlbox-button-with-hole.stl
36.0 x 36.0 x 13.8
