dallaszkorben/diy-greenwall/3D/STL/owerflow/overflow_ring.stl

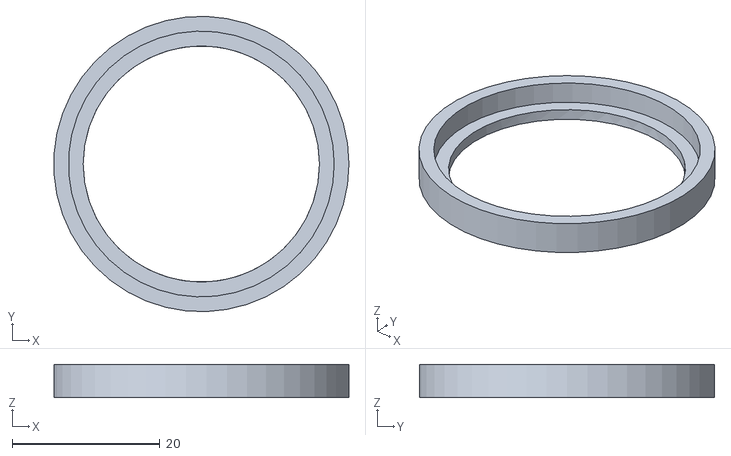
[picture p87: CAD file, 2022-04-15]
3D/STL/owerflow/overflow_ring.stl
40.0 x 40.0 x 4.50
