dallaszkorben/diy-greenwall/3D/STL/pipe/pipe.clamp-frane.stl

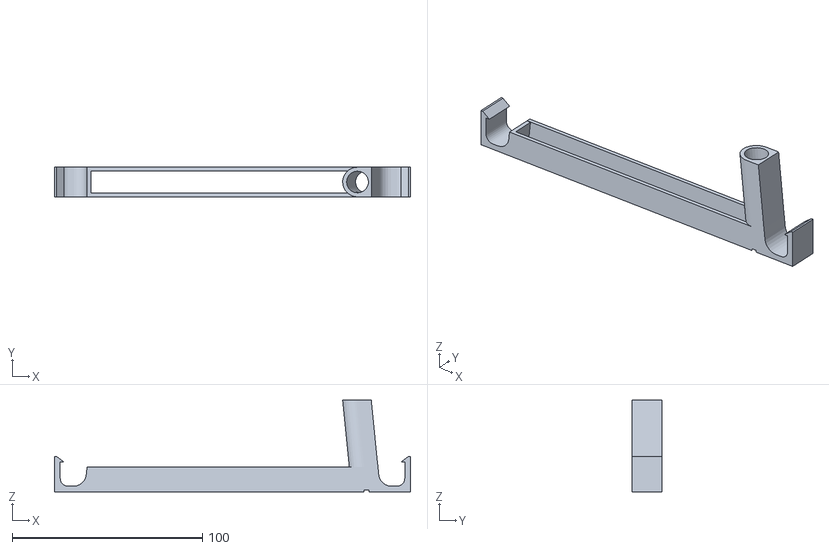
[picture p88: CAD file, 2021-09-19]
3D/STL/pipe/pipe.clamp-frane.stl
187.2 x 15.6 x 48.2
