dallaszkorben/diy-greenwall/3D/STL/station.lamp/station.lamp.2x42v-YL401.3mf

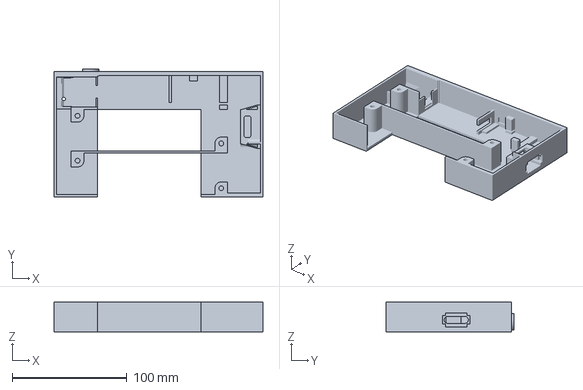
[picture p89: CAD file, 2024-05-13]
3D/STL/station.lamp/station.lamp.2x42v-YL401.3mf
181.8 x 111.1 x 26.0 mm
