dallaszkorben/diy-greenwall/3D/FREECAD/hanger.sonic.sensor.FCStd

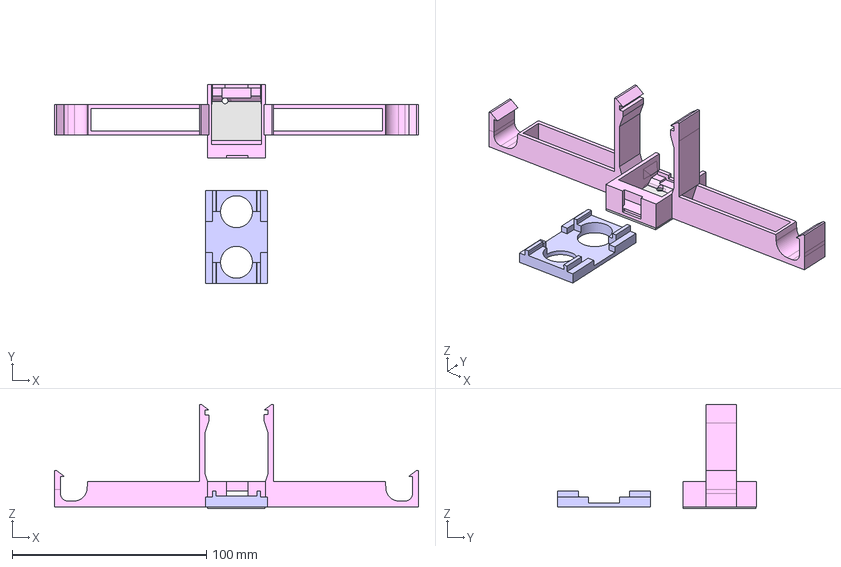
[picture p90: CAD file, 2021-12-12]
3D/FREECAD/hanger.sonic.sensor.FCStd
187.2 x 102.5 x 53.7 mm
