dallaszkorben/diy-greenwall/3D/FREECAD/station.lamp.pump/control.station.lamp.pump_jack.FCStd

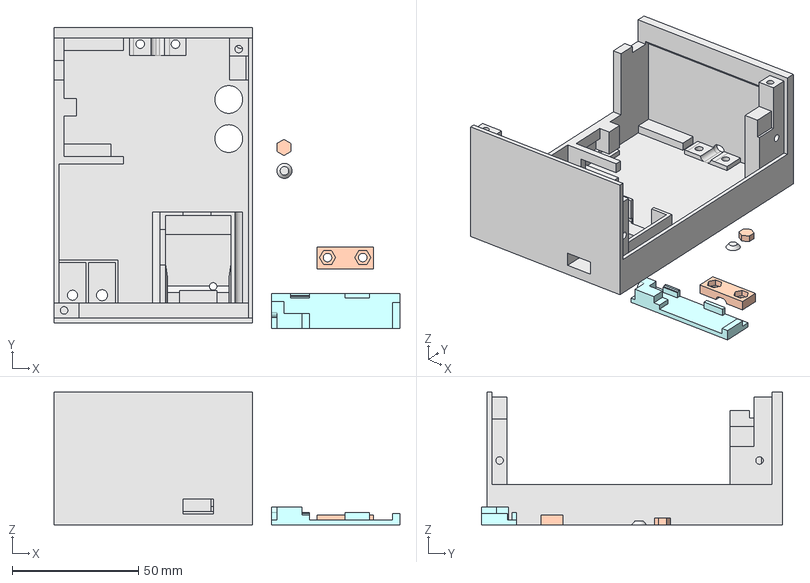
[picture p91: CAD file, 2022-08-14]
3D/FREECAD/station.lamp.pump/control.station.lamp.pump_jack.FCStd
137.1 x 119.1 x 52.6 mm
