dallaszkorben/diy-greenwall/3D/STL/camera/camera.wroover.nested_console.long.stl

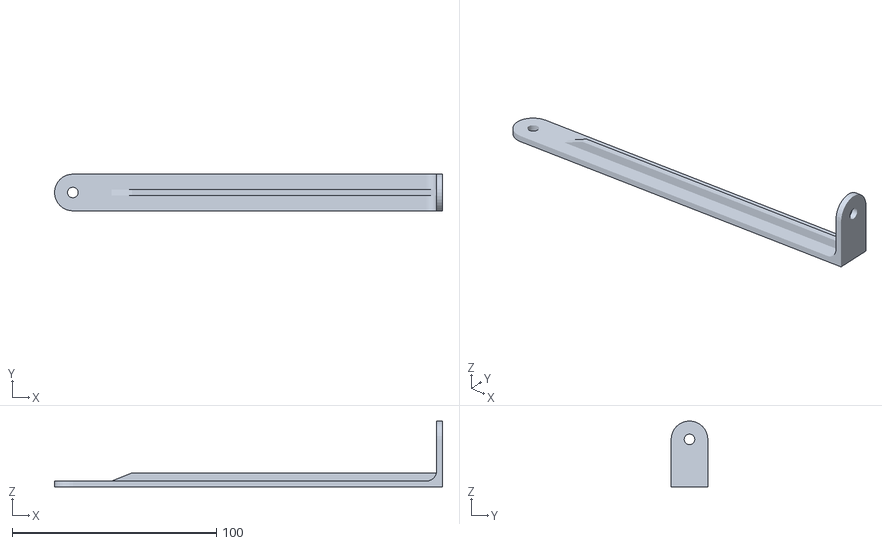
[picture p92: CAD file, 2022-10-02]
3D/STL/camera/camera.wroover.nested_console.long.stl
190.0 x 18.0 x 32.3
