dallaszkorben/diy-greenwall/3D/STL/pipe/pipe.clamp.stl

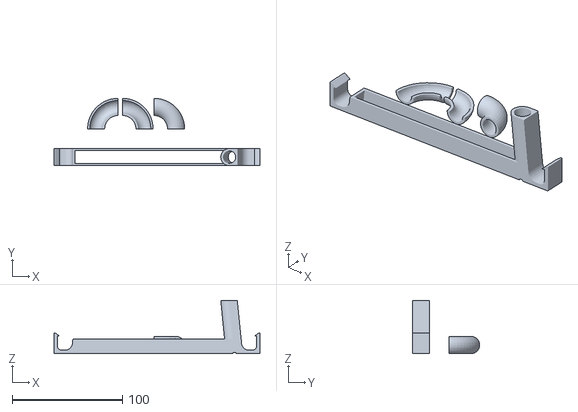
[picture p93: CAD file, 2021-09-12]
3D/STL/pipe/pipe.clamp.stl
187.2 x 61.2 x 48.3
