dallaszkorben/diy-greenwall/3D/STL/camera/camera.wroover_rail_.reverse.stl

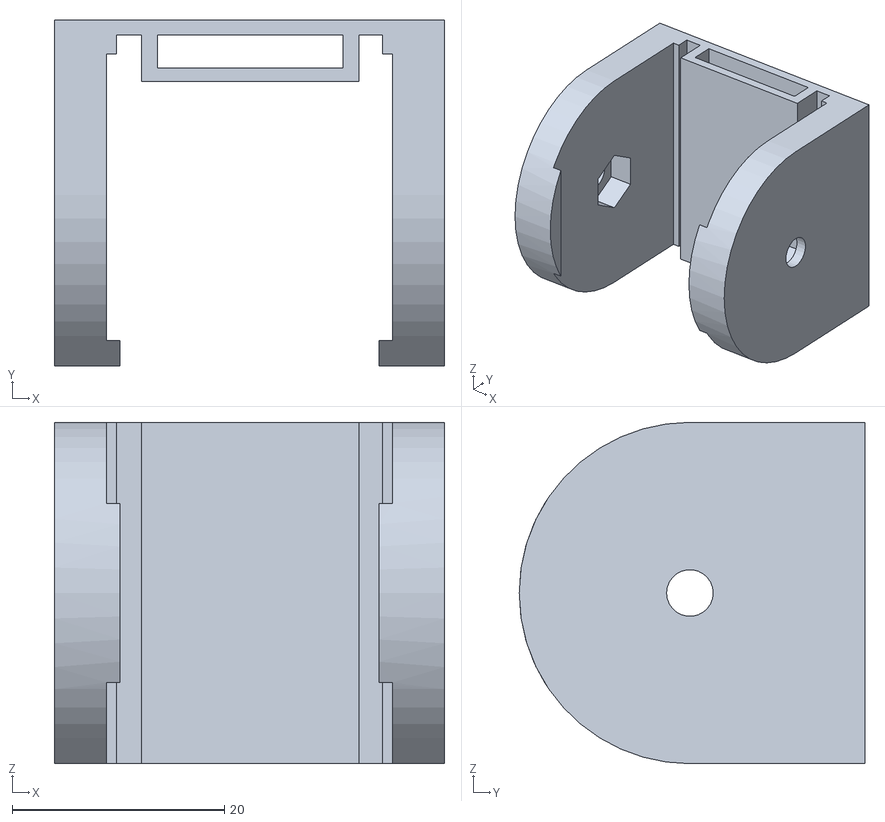
[picture p94: CAD file, 2022-10-02]
3D/STL/camera/camera.wroover_rail_.reverse.stl
36.8 x 32.6 x 32.2
