dallaszkorben/diy-greenwall/3D/STL/container/container.V3.stl

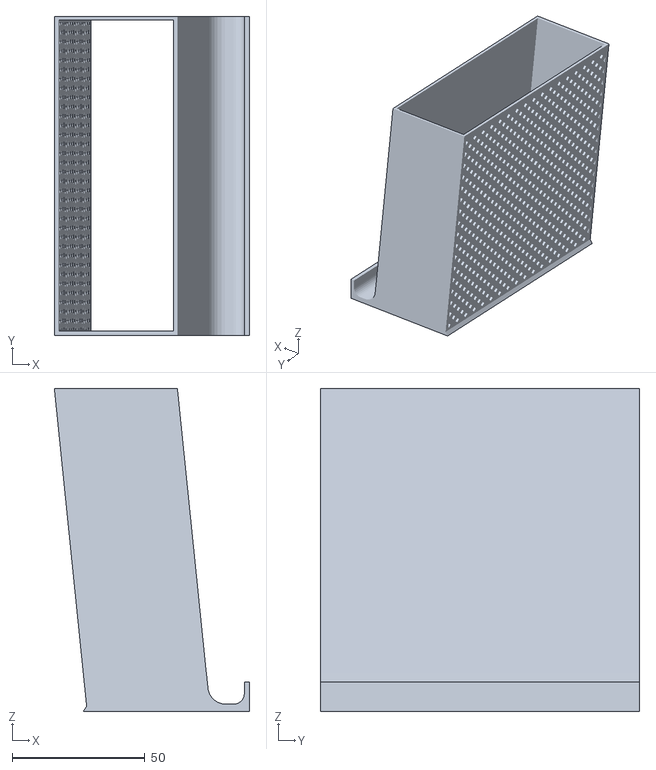
[picture p95: CAD file, 2021-09-12]
3D/STL/container/container.V3.stl
73.5 x 120.0 x 121.6
