dallaszkorben/diy-greenwall/3D/STL/lamp.hanger/lamp.hanger_cap_reverse_closed.stl

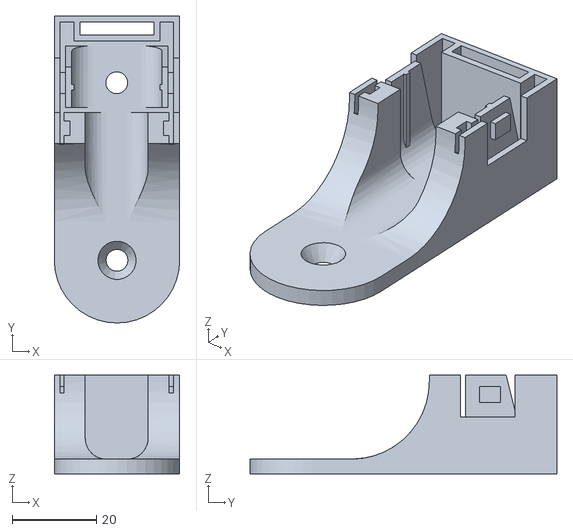
[picture p96: CAD file, 2022-08-27]
3D/STL/lamp.hanger/lamp.hanger_cap_reverse_closed.stl
29.9 x 73.1 x 23.5
