dallaszkorben/diy-greenwall/3D/STL/owerflow/overflow_pipe.stl

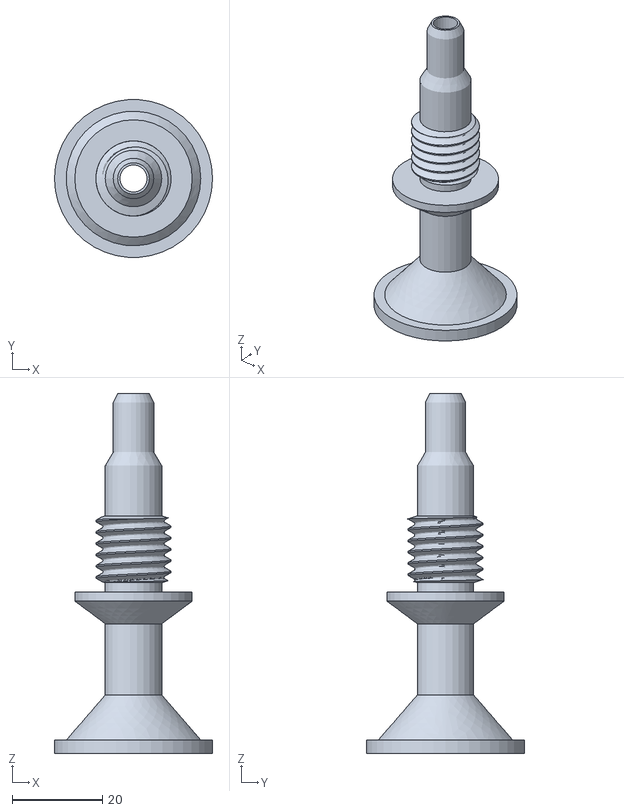
[picture p97: CAD file, 2022-04-14]
3D/STL/owerflow/overflow_pipe.stl
35.0 x 34.9 x 79.7
