dallaszkorben/diy-greenwall/3D/STL/pipe/pipe.clamp-curve.part.stl

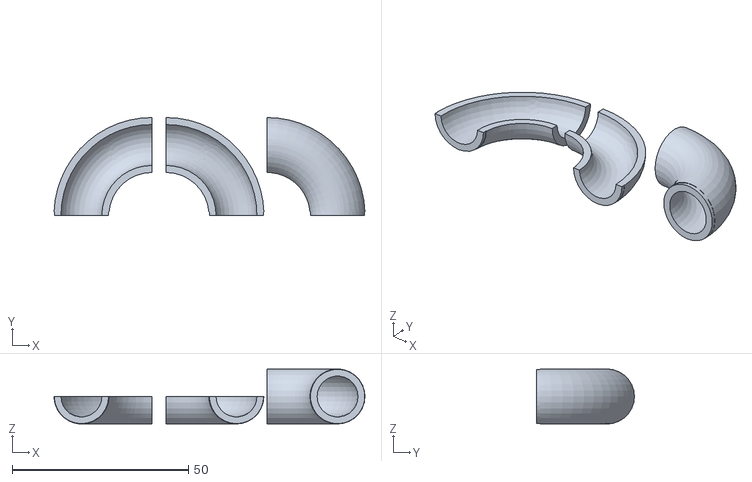
[picture p98: CAD file, 2021-09-12]
3D/STL/pipe/pipe.clamp-curve.part.stl
88.2 x 27.8 x 15.6
