dallaszkorben/diy-greenwall/3D/STL/camera/camera.wroover.cover.stl

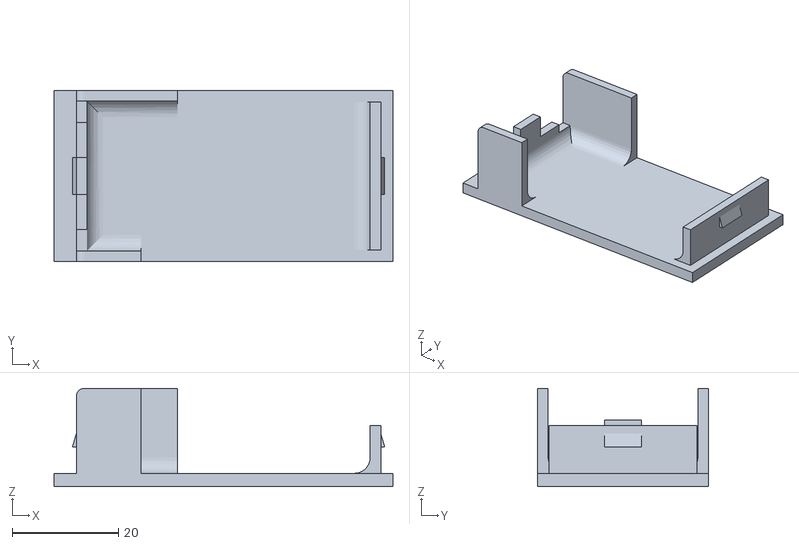
[picture p99: CAD file, 2022-09-24]
3D/STL/camera/camera.wroover.cover.stl
63.8 x 32.2 x 18.5
