dallaszkorben/diy-greenwall/3D/STL/pipe/pipe.clamp.V2.stl

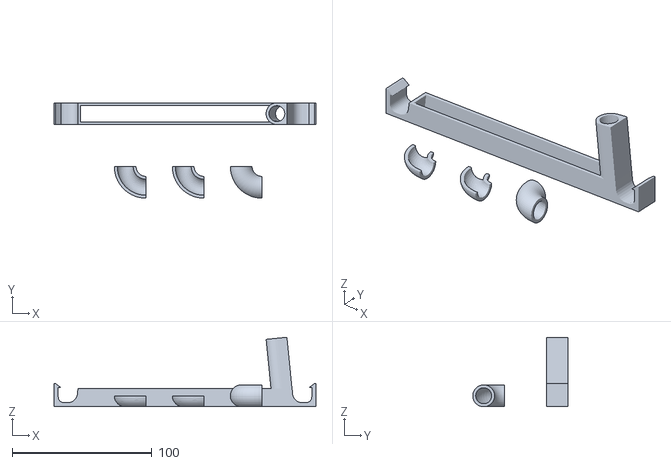
[picture p100: CAD file, 2021-09-12]
3D/STL/pipe/pipe.clamp.V2.stl
187.2 x 68.2 x 49.6
