dallaszkorben/diy-greenwall/3D/STL/camera/camera.wroover.buttons.stl

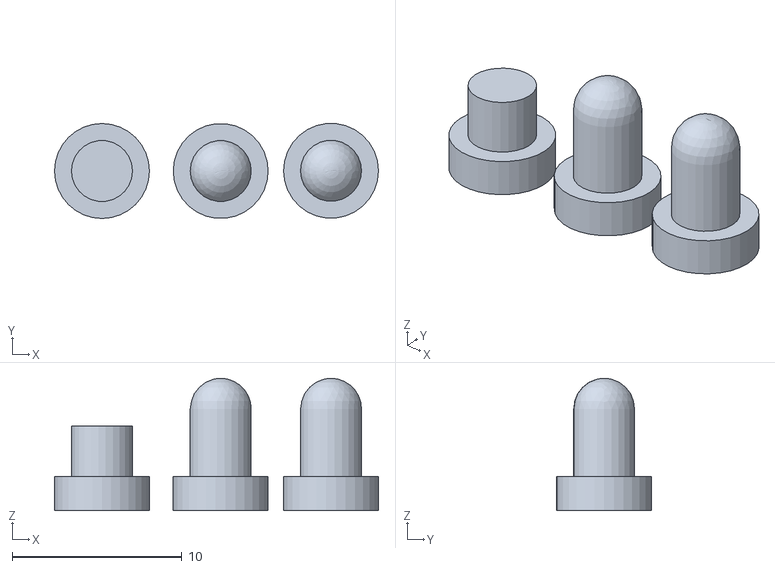
[picture p101: CAD file, 2022-09-24]
3D/STL/camera/camera.wroover.buttons.stl
19.1 x 5.60 x 7.80
