dallaszkorben/diy-greenwall/3D/STL/camera/camera.wroover.all.reverse.stl

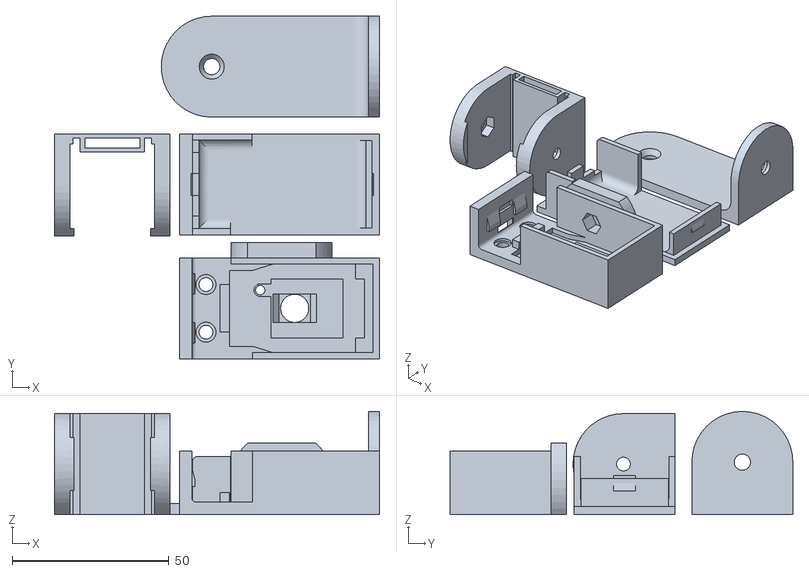
[picture p102: CAD file, 2022-09-24]
3D/STL/camera/camera.wroover.all.reverse.stl
103.6 x 109.3 x 32.9
