dallaszkorben/diy-greenwall/3D/STL/camera/camera.wroover_frame.stl

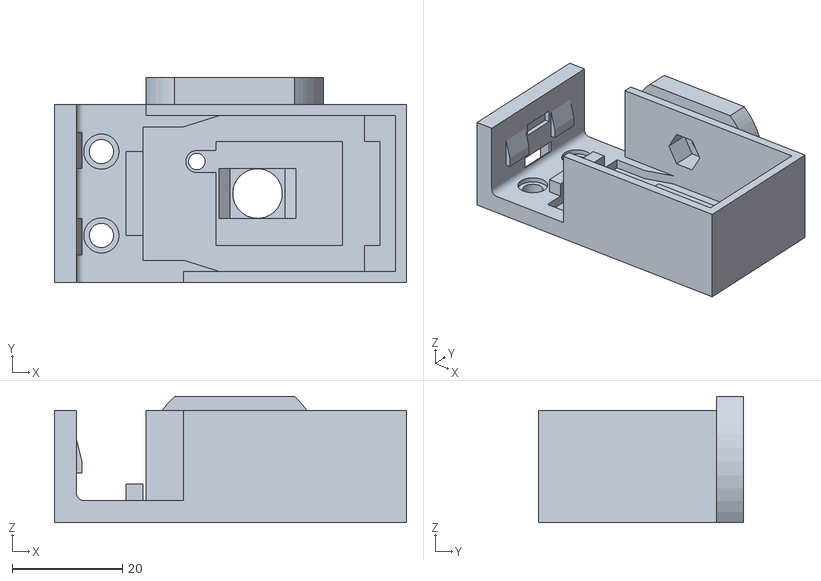
[picture p103: CAD file, 2022-09-24]
3D/STL/camera/camera.wroover_frame.stl
63.8 x 37.1 x 22.8
