dallaszkorben/diy-greenwall/3D/STL/camera/camera.wroover.all.straight.stl

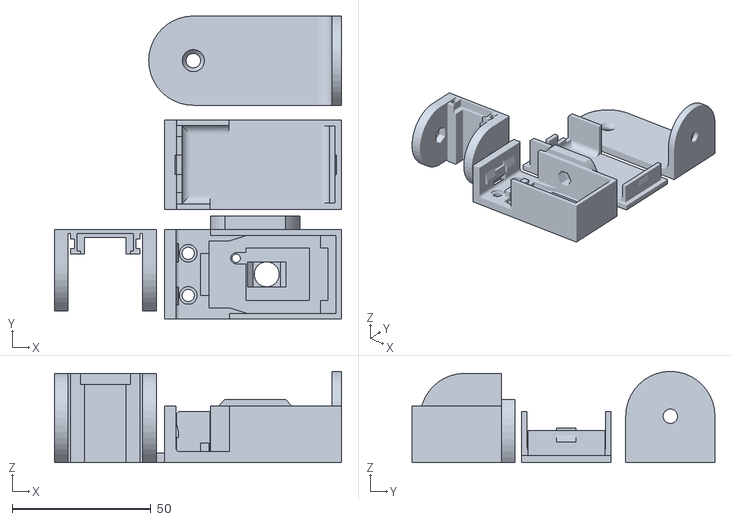
[picture p104: CAD file, 2022-09-24]
3D/STL/camera/camera.wroover.all.straight.stl
103.6 x 109.3 x 32.9
