dallaszkorben/diy-greenwall/3D/STL/camera/camera.wroover_rail_.straight.stl

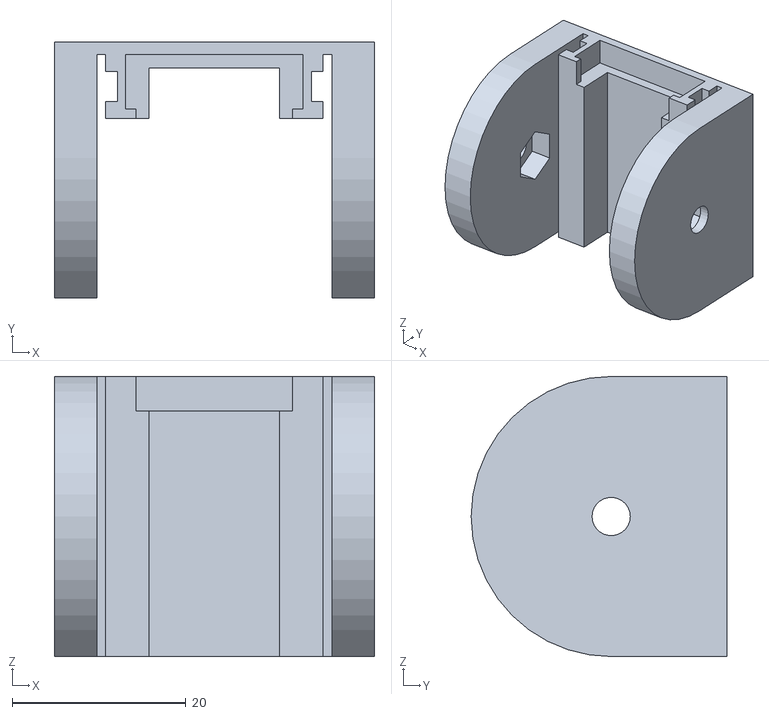
[picture p105: CAD file, 2022-09-19]
3D/STL/camera/camera.wroover_rail_.straight.stl
36.8 x 29.4 x 32.2
