dallaszkorben/diy-greenwall/3D/STL/camera/camera.wroover.console.stl

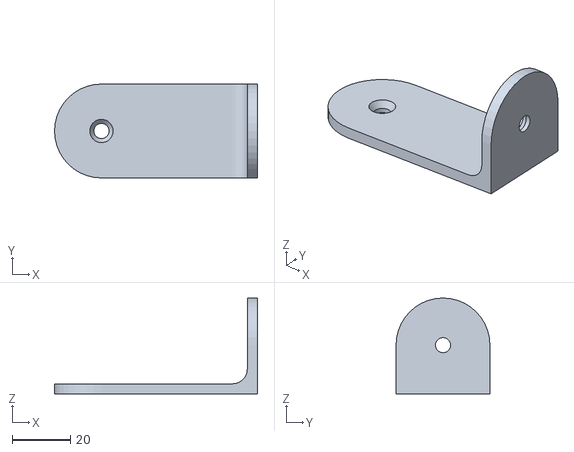
[picture p106: CAD file, 2022-09-19]
3D/STL/camera/camera.wroover.console.stl
69.6 x 32.2 x 32.9
