dallaszkorben/diy-greenwall/3D/FREECAD/spacer.FCStd

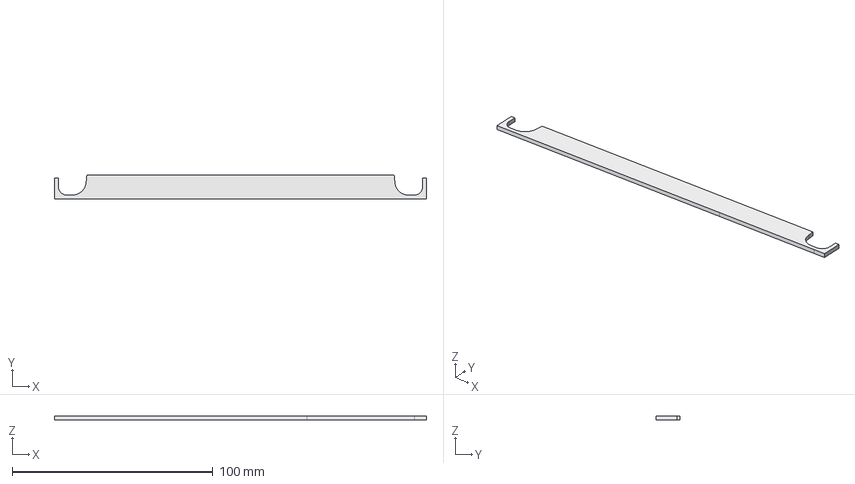
[picture p107: CAD file, 2021-09-12]
3D/FREECAD/spacer.FCStd
185.2 x 12.1 x 2.00 mm
