dallaszkorben/diy-greenwall/3D/FREECAD/container.FCStd

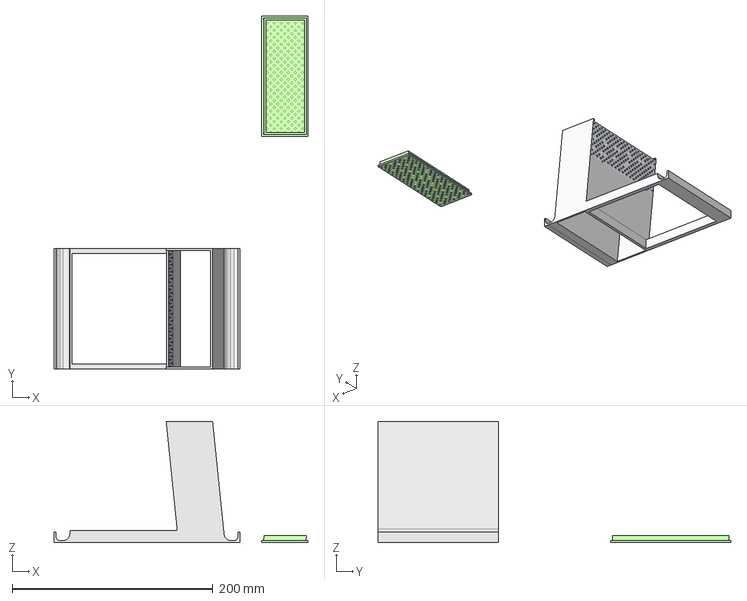
[picture p108: CAD file, 2021-09-12]
3D/FREECAD/container.FCStd
253.1 x 351.5 x 120.8 mm
