dallaszkorben/diy-greenwall/Software/Control.Station_Sensors/ESP12F/C/ControlStation_Sensor-HC-SR04/HTTPServer.ino

#include <ArduinoJson.h>

//--- define functions ---
double getAvgTemp();
boolean isDecimal(String str);
boolean isInteger(String str);
boolean isBoolean(String str);
static bool ToBoolean(String str);
void persistVariables();

void handleNotFound(){

  server.send(404, "text/plain", "404: Not found");

  Serial.println("!!! HTTP request was not found !!!");
  Serial.println();
}

void handleGetConfigure(){
  DynamicJsonDocument result(512);
  String buf;

  Serial.print("'GET /configure' request - ");

  result["success"] = true;
  result["status"] = "OK";
  result["message"] = "OK";

  result["data"]["version"] = version;

  result["data"]["stationId"] = stationId;

  result["data"]["sensorTempHumOutGPIO"] = sensorTempHumOutGPIO;
  result["data"]["sensorDistanceTrigGPIO"] = sensorDistanceTrigGPIO;
  result["data"]["sensorDistanceEchoGPIO"] = sensorDistanceEchoGPIO;

  result["data"]["sensorDistanceParA"] = sensorDistanceParA;
  result["data"]["sensorDistanceParB"] = sensorDistanceParB;
  result["data"]["sensorDistanceParC"] = sensorDistanceParC;

  result["data"]["intervalReportMillis"] = intervalReportMillis;
  result["data"]["intervalRegisterMillis"] = intervalRegisterMillis;
  result["data"]["intervalResetMillis"] = intervalResetMillis;
  result["data"]["intervalConnectionMillis"] = intervalConnectionMillis;

  result["data"]["needToReport"] = needToReport;

  serializeJson(result, buf);
  server.send(200, "application/json", buf);

  Serial.println("Served:");
  Serial.print("        ");
  Serial.println(String(result["data"]));
}

void handlePostConfigure(){
  Serial.print("'POST /configure' request - ");

  String resultJson;
  String postBody = server.arg("plain");
  Serial.println(postBody);

  DynamicJsonDocument result(512);
  String buf;
  DynamicJsonDocument doc(512);
  DeserializationError error = deserializeJson(doc, postBody);
  if (error) {

    // if the file didn't open, print an error:
    String msg = error.c_str();
    Serial.print("Error parsing JSON: ");
    Serial.println(msg);

    result["status"] = "ERROR";
    result["message"] = msg;
    serializeJson(result, buf);
    server.send(400, "application/json", buf);

  } else {

    int resultCode;
    boolean updateNeeded = false;

    String errorStationId = "";
    String errorSensorTempHumOutGPIO = "";
    String errorSensorDistanceTrigGPIO = "";
    String errorSensorDistanceEchoGPIO = "";
    String errorSensorDistanceParA = "";
    String errorSensorDistanceParB = "";
    String errorSensorDistanceParC = "";

    String errorIntervalReportMillis = "";
    String errorIntervalRegisterMillis = "";
    String errorIntervalResetMillis = "";
    String errorIntervalConnectionMillis = "";

    String errorNeedToReport = "";

    JsonObject postObj = doc.as<JsonObject>();
    Serial.println("Json parameters are successfully parsed");

    //
    // stationId
    //
    const char* myStationId = postObj["stationId"];
    if(myStationId){
      String strStationId = String(myStationId);
      strStationId.trim();
      if(strStationId.length() == 0 || strStationId.indexOf(" ") >= 0){
        errorStationId = "Wrong value: '" + strStationId + "'. " + ((strStationId.length() == 0) ? "Empty" : "Contains space");
        Serial.println(errorStationId);
      }else{
        stationId = strStationId;
        updateNeeded = true;
      }
    }else{
      Serial.println("NO stationId modified");
    }

    //
    // sensorTempHumOutGPIO
    //
    const char* mySensorTempHumOutGPIO = postObj["sensorTempHumOutGPIO"];
    if(mySensorTempHumOutGPIO){
      if(isInteger(String(mySensorTempHumOutGPIO))){
        int intSensorTempHumOutGPIO = atoi(mySensorTempHumOutGPIO);
        if(intSensorTempHumOutGPIO < 0 || intSensorTempHumOutGPIO >= 15){
          errorSensorTempHumOutGPIO = "Wrong value: '" + String(mySensorTempHumOutGPIO) + "'. " + ((intSensorTempHumOutGPIO <= 0) ? " < 0" : " > 15");
          Serial.println(errorSensorTempHumOutGPIO);
        }else{
          sensorTempHumOutGPIO = intSensorTempHumOutGPIO;
          updateNeeded = true;
        }
      }else{
        errorSensorTempHumOutGPIO = "Wrong value in 'sensorTempHumOutGPIO': '" + String(mySensorTempHumOutGPIO) + "' is NOT an Integer.";
        Serial.println(errorSensorTempHumOutGPIO);
      }
    }else{
      Serial.println("NO sensorTempHumOutGPIO modified");
    }

    //
    // sensorDistanceTrigGPIO
    //
    const char* mySensorDistanceTrigGPIO = postObj["sensorDistanceTrigGPIO"];
    if(mySensorDistanceTrigGPIO){
      if(isInteger(String(mySensorDistanceTrigGPIO))){
        int intSensorDistanceTrigGPIO = atoi(mySensorDistanceTrigGPIO);
        if(intSensorDistanceTrigGPIO < 0 || intSensorDistanceTrigGPIO >= 15){
          errorSensorDistanceTrigGPIO = "Wrong value: '" + String(mySensorDistanceTrigGPIO) + "'. " + ((intSensorDistanceTrigGPIO <= 0) ? " < 0" : " > 15");
          Serial.println(errorSensorDistanceTrigGPIO);
        }else{
          sensorDistanceTrigGPIO = intSensorDistanceTrigGPIO;        
          updateNeeded = true;
        }
      }else{
        errorSensorDistanceTrigGPIO = "Wrong value in 'sensorDistanceTrigGPIO': '" + String(mySensorDistanceTrigGPIO) + "' is NOT an Integer.";
        Serial.println(errorSensorDistanceTrigGPIO);
      }
    }else{
      Serial.println("NO sensorDistanceTrigGPIO modified");
    }

    //
    // sensorDistanceTrigGPIO
    //
    const char* mySensorDistanceEchoGPIO = postObj["sensorDistanceEchoGPIO"];        
    if(mySensorDistanceEchoGPIO){
      if(isInteger(String(mySensorDistanceEchoGPIO))){
        int intSensorDistanceEchoGPIO = atoi(mySensorDistanceEchoGPIO);      
        if(intSensorDistanceEchoGPIO < 0 || intSensorDistanceEchoGPIO >= 15){
          errorSensorDistanceEchoGPIO = "Wrong value: '" + String(mySensorDistanceEchoGPIO) + "'. " + ((intSensorDistanceEchoGPIO <= 0) ? " < 0" : " > 15");
          Serial.println(errorSensorDistanceEchoGPIO);
        }else{
          sensorDistanceEchoGPIO = intSensorDistanceEchoGPIO;        
          updateNeeded = true;
        }
      }else{
        errorSensorDistanceTrigGPIO = "Wrong value in 'sensorDistanceEchoGPIO': '" + String(mySensorDistanceEchoGPIO) + "' is NOT an Integer.";
        Serial.println(errorSensorDistanceEchoGPIO);
      }
    }else{
      Serial.println("NO sensorDistanceEchoGPIO modified");
    }
    
    //
    // sensorDistanceParA
    //
    const char* mySensorDistanceParA = postObj["sensorDistanceParA"];        
    if(mySensorDistanceParA){
      if(isDecimal(String(mySensorDistanceParA))){
        sensorDistanceParA = String(mySensorDistanceParA).toDouble();
        updateNeeded = true;
      }else{
        errorSensorDistanceParA = "Wrong value in 'sensorDistanceParA': '" + String(mySensorDistanceParA) + "' is NOT an Double.";
        Serial.println(errorSensorDistanceParA);
      }
    }else{
      Serial.println("NO sensorDistanceParA modified");
    }    

    //
    // sensorDistanceParB
    //
    const char* mySensorDistanceParB = postObj["sensorDistanceParB"];
    if(mySensorDistanceParB){
      if(isDecimal(String(mySensorDistanceParB))){
        sensorDistanceParB = String(mySensorDistanceParB).toDouble();
        updateNeeded = true;
      }else{
        errorSensorDistanceParB = "Wrong value in 'sensorDistanceParB': '" + String(mySensorDistanceParB) + "' is NOT an Double.";
        Serial.println(errorSensorDistanceParB);
      }
    }else{
      Serial.println("NO sensorDistanceParB modified");
    }    

    //
    // sensorDistanceParC
    //
    const char* mySensorDistanceParC = postObj["sensorDistanceParC"];
    if(mySensorDistanceParC){
      if(isDecimal(String(mySensorDistanceParC))){
        sensorDistanceParC = String(mySensorDistanceParC).toDouble();
        updateNeeded = true;
      }else{
        errorSensorDistanceParC = "Wrong value in 'sensorDistanceParC': '" + String(mySensorDistanceParC) + "' is NOT an Double.";
        Serial.println(errorSensorDistanceParC);
      }
    }else{
      Serial.println("NO sensorDistanceParC modified");
    }    

    //
    // intervalReportMillis
    //
    const char* myIntervalReportMillis = postObj["intervalReportMillis"];        
    if(myIntervalReportMillis){
      if(isInteger(String(myIntervalReportMillis))){
        unsigned long ulIntervalReportMillis = strtoul(myIntervalReportMillis, NULL, 0);      
        if(ulIntervalReportMillis < 60000){
          errorIntervalReportMillis = "Wrong value: '" + String(myIntervalReportMillis) + "'. " + " < 60000 (1 minute)";
          Serial.println(errorIntervalReportMillis);
        }else{
          intervalReportMillis = ulIntervalReportMillis;        
          updateNeeded = true;
        }
      }else{
        errorIntervalReportMillis = "Wrong value in 'intervalReportMillis': '" + String(myIntervalReportMillis) + "' is NOT a Long.";
        Serial.println(errorIntervalReportMillis);
      }
    }else{
      Serial.println("NO intervalReportMillis modified");
    }

    //
    // intervalRegisterMillis
    //
    const char* myIntervalRegisterMillis = postObj["intervalRegisterMillis"];        
    if(myIntervalRegisterMillis){
      if(isInteger(String(myIntervalRegisterMillis))){
        unsigned long ulIntervalRegisterMillis = strtoul(myIntervalRegisterMillis, NULL, 0);      
        if(ulIntervalRegisterMillis < 60000){
          errorIntervalRegisterMillis = "Wrong value: '" + String(myIntervalRegisterMillis) + "'. " + " < 60000 (1 minute)";
          Serial.println(errorIntervalRegisterMillis);
        }else{
          intervalRegisterMillis = ulIntervalRegisterMillis;        
          updateNeeded = true;
        }
      }else{
        errorIntervalRegisterMillis = "Wrong value in 'intervalRegisterMillis': '" + String(myIntervalRegisterMillis) + "' is NOT a Long.";
        Serial.println(errorIntervalRegisterMillis);
      }
    }else{
      Serial.println("NO intervalRegisterMillis modified");
    }

    //
    // intervalResetMillis
    //
    const char* myIntervalResetMillis = postObj["intervalResetMillis"];
    if(myIntervalResetMillis){
      if(isInteger(String(myIntervalResetMillis))){
        unsigned long ulIntervalResetMillis = strtoul(myIntervalResetMillis, NULL, 0);
        if(ulIntervalResetMillis < 60000){
          errorIntervalResetMillis = "Wrong value: '" + String(myIntervalResetMillis) + "'. " + " < 60000 (1 minute)";
          Serial.println(errorIntervalResetMillis);
        }else{
          intervalResetMillis = ulIntervalResetMillis;
          updateNeeded = true;
        }
      }else{
        errorIntervalResetMillis = "Wrong value in 'intervalResetMillis': '" + String(myIntervalResetMillis) + "' is NOT a Long.";
        Serial.println(errorIntervalResetMillis);
      }
    }else{
      Serial.println("NO intervalResetMillis modified");
    }

    //
    // intervalConnectionMillis
    //
    const char* myIntervalConnectionMillis = postObj["intervalConnectionMillis"];
    if(myIntervalConnectionMillis){
      if(isInteger(String(myIntervalConnectionMillis))){
        unsigned long ulIntervalConnectionMillis = strtoul(myIntervalConnectionMillis, NULL, 0);
        if(ulIntervalConnectionMillis < 60000){
          errorIntervalConnectionMillis = "Wrong value: '" + String(myIntervalConnectionMillis) + "'. " + " < 60000 (1 minute)";
          Serial.println(errorIntervalConnectionMillis);
        }else{
          intervalConnectionMillis = ulIntervalConnectionMillis;
          updateNeeded = true;
        }
      }else{
        errorIntervalConnectionMillis = "Wrong value in 'intervalConnectionMillis': '" + String(myIntervalConnectionMillis) + "' is NOT a Long.";
        Serial.println(errorIntervalConnectionMillis);
      }
    }else{
      Serial.println("NO intervalConnectionMillis modified");
    }

    //
    // needToReport
    //
    const char* myNeedToReport = postObj["needToReport"];
    if(myNeedToReport){
      if(isBoolean(String(myNeedToReport))){
        needToReport = ToBoolean(myNeedToReport);
        updateNeeded = true;
      }else{
        errorNeedToReport = "Wrong value in 'needToReport': '" + String(myNeedToReport) + "' is NOT an Boolean.";
        Serial.println(errorNeedToReport);
      }
    }else{
      Serial.println("NO needToReport modified");
    }

    // If there was at least 1 wrong (existing) parameter
    if(errorStationId.length()!=0 || errorSensorTempHumOutGPIO.length() != 0 || errorSensorDistanceTrigGPIO.length() != 0 || errorSensorDistanceParA.length() != 0 || errorSensorDistanceParB.length() != 0 || errorSensorDistanceParC.length() != 0 || errorIntervalReportMillis.length() != 0 || errorIntervalRegisterMillis.length() != 0 || errorIntervalResetMillis.length() != 0 || errorIntervalConnectionMillis.length() != 0 || errorNeedToReport.length() != 0){
      resultCode = 400;
      if(errorStationId.length()!=0){
        result["success"] = false;
        result["status"] = "ERROR";
        result["message"] = "Wrong parameter(s) provided";
        result["data"]["stationId"] = errorStationId;
      }
      if(errorSensorTempHumOutGPIO.length() != 0){
        result["success"] = false;
        result["status"] = "ERROR";
        result["message"] = "Wrong parameter(s) provided";
        result["data"]["sensorTempHumOutGPIO"] = errorSensorTempHumOutGPIO;
      }
      if(errorSensorDistanceTrigGPIO.length() != 0){
        result["success"] = false;
        result["status"] = "ERROR";
        result["message"] = "Wrong parameter(s) provided";
        result["data"]["sensorDistanceTrigGPIO"] = errorSensorDistanceTrigGPIO;
      }
      if(errorSensorDistanceParA.length() != 0){
        result["success"] = false;
        result["status"] = "ERROR";
        result["message"] = "Wrong parameter(s) provided";
        result["data"]["sensorDistanceParA"] = errorSensorDistanceParA;
      }
      if(errorSensorDistanceParB.length() != 0){
        result["success"] = false;
        result["status"] = "ERROR";
        result["message"] = "Wrong parameter(s) provided";
        result["data"]["sensorDistanceParB"] = errorSensorDistanceParB;
      }
      if(errorSensorDistanceParC.length() != 0){
        result["success"] = false;
        result["status"] = "ERROR";
        result["message"] = "Wrong parameter(s) provided";
        result["data"]["sensorDistanceParC"] = errorSensorDistanceParC;
      }
      if(errorIntervalReportMillis.length() != 0){
        result["success"] = false;
        result["status"] = "ERROR";
        result["message"] = "Wrong parameter(s) provided";
        result["data"]["intervalReportMillis"] = errorIntervalReportMillis;
      }
      if(errorIntervalRegisterMillis.length() != 0){
        result["success"] = false;
        result["status"] = "ERROR";
        result["message"] = "Wrong parameter(s) provided";
        result["data"]["intervalRegisterMillis"] = errorIntervalRegisterMillis;
      }
      if(errorIntervalResetMillis.length() != 0){
        result["success"] = false;
        result["status"] = "ERROR";
        result["message"] = "Wrong parameter(s) provided";
        result["data"]["intervalResetMillis"] = errorIntervalResetMillis;
      }
      if(errorIntervalConnectionMillis.length() != 0){
        result["success"] = false;
        result["status"] = "ERROR";
        result["message"] = "Wrong parameter(s) provided";
        result["data"]["intervalConnectionMillis"] = errorIntervalConnectionMillis;
      }
      if(errorNeedToReport.length() != 0){
        result["success"] = false;
        result["status"] = "ERROR";
        result["message"] = "Wrong parameter(s) provided";
        result["data"]["needToReport"] = errorNeedToReport;
      }

    // No error in the existing provided parameters
    }else if(updateNeeded){
      resultCode = 201;
      result["success"] = true;
      result["status"] = "OK";
      result["message"] = "OK";

      persistVariables();

    // No existing parameter was provided
    }else{
      resultCode = 400;
      result["success"] = false;
      result["status"] = "ERROR";
      result["message"] = "No existing parameter was provided";
    }

    serializeJson(result, buf);
    server.send(resultCode, "application/json", buf);
  }
  Serial.println("Served");

}

void handleGetPressure(){
  DynamicJsonDocument result(512);
  String buf;

  Serial.print("'GET /pressure' request - ");

  struct BMP180_Struct bmp180Result = getPressTemp(false); //getSampleOfPressTemp(1);
  double pressure = bmp180Result.pressure;

  result["success"] = true;
  result["status"] = "OK";
  result["message"] = "OK";
  result["data"]["pressure"] = String(pressure);

  serializeJson(result, buf);
  server.send(200, "application/json", buf);

  Serial.println("Served");
}

void handleGetTemperature(){
  DynamicJsonDocument result(512);
  String buf;

  Serial.print("'GET /tepmerature' request - ");

  struct BMP180_Struct bmp180Result = getSampleOfPressTemp(1); //getPressTemp(false);
  double temp1 = bmp180Result.temperature;

  struct DHT_Struct dhtResult = getSampleOfTempHum(1);
  double temp2 = dhtResult.temperature;

  double temperature = getAvgTemp(temp1, temp2);

  result["success"] = true;
  result["status"] = "OK";
  result["message"] = "OK";
  result["data"]["temperature"] = String(temperature);

  serializeJson(result, buf);
  server.send(200, "application/json", buf);

  Serial.println("Served");
}

void handleGetHumidity(){
  DynamicJsonDocument result(512);
  String buf;

  Serial.print("'GET /humidity' request - ");

  struct DHT_Struct dhtResult = getTempHum(false); //getSampleOfTempHum(1);

  result["success"] = true;
  result["status"] = "OK";
  result["message"] = "OK";
  result["data"]["humidity"] = String(dhtResult.humidity);

  serializeJson(result, buf);
  server.send(200, "application/json", buf);

  Serial.println("Served");
  Serial.println();
}

void handleGetDistance(){
  DynamicJsonDocument result(512);
  String buf;

  Serial.print("'GET /distance' request - ");

  double distance = getDistanceByDuration(getDuration(false)); //getSampleOfDistance(1);

  result["success"] = true;
  result["status"] = "OK";
  result["message"] = "OK";
  result["data"]["distance"] = String(distance);

  serializeJson(result, buf);
  server.send(200, "application/json", buf);

  Serial.println("Served");
}

void handleGetDuration(){
  DynamicJsonDocument result(512);
  String buf;

  Serial.print("'GET /duration' request - ");

  double duration = getDuration(false);

  result["success"] = true;
  result["status"] = "OK";
  result["message"] = "OK";
  result["data"]["duration"] = String(duration);

  serializeJson(result, buf);
  server.send(200, "application/json", buf);

  Serial.println("Served");
}

void handleGetAllActual(){
  DynamicJsonDocument result(512);
  String buf;

  Serial.print("'GET /all/actual' request - ");

  //===
  struct BMP180_Struct bmp180Result = getPressTemp(false); //getSampleOfPressTemp(1);
  double pressure = bmp180Result.pressure;
  //---
  double temp1 = bmp180Result.temperature;

  struct DHT_Struct dhtResult = getTempHum(false);
  double temp2 = dhtResult.temperature;

  double temperature = getAvgTemp(temp1, temp2);
  //---
  double humidity = dhtResult.humidity;
  //---
  double distance = getDistanceByDuration(getDuration(false));
  //===

  result["success"] = true;
  result["status"] = "OK";
  result["message"] = "OK";
  result["data"]["temperature"] = String(temperature);
  result["data"]["humidity"] = String(humidity);
  result["data"]["pressure"] = String(pressure);
  result["data"]["distance"] = String(distance);

  serializeJson(result, buf);
  server.send(200, "application/json", buf);

  Serial.println("Served");
}

void handleGetAllAggregated(){
  DynamicJsonDocument result(512);
  String buf;

  Serial.print("'GET /all/aggregated' request - ");

  String levelValue = (avgHcsrDist != NULL) ? String(avgHcsrDist) : "";
  String pressureValue = (avgBmpPress != NULL) ? String(avgBmpPress) : "";
  String humidityValue = (avgDhtHum != NULL) ? String(avgDhtHum) : "";

  double temp1 = avgBmpTemp;
  double temp2 = avgDhtTemp;
  double avgTemp = getAvgTemp(temp1, temp2);

  String temperatureValue = (avgTemp != NULL) ? String(avgTemp) : "";

  result["success"] = true;
  result["status"] = "OK";
  result["message"] = "OK";
  result["data"]["temperature"] = temperatureValue;
  result["data"]["humidity"] = humidityValue;
  result["data"]["pressure"] = pressureValue;
  result["data"]["distance"] = levelValue;

  serializeJson(result, buf);
  server.send(200, "application/json", buf);

  Serial.println("Served");
}

void handleTriggerReport(){
    DynamicJsonDocument result(512);
    String buf;
    int resultCode;

    Serial.print("'POST /trigger/report' request - ");

    if ( reportSensors(true) ){
        Serial.print("Sensors was reported at ");
        Serial.println(getOffsetDateString());
        previousReportMillis = currentMillis;

        result["success"] = true;
        result["status"] = "OK";
        result["message"] = "OK";

        resultCode = 200;
    }else{
        ledSignalNetworkError();
        Serial.print("!!! Sensors report failed at: ");
        Serial.println(getOffsetDateString());

        result["success"] = true;
        result["status"] = "FAIL";
        result["message"] = "Sensors report failed";

        resultCode = 500;
    }

    serializeJson(result, buf);
    server.send(resultCode, "application/json", buf);

    Serial.print("Result: ");
    Serial.println(String(result["message"]));
}


bool configureHttpServer(){
  bool ret = true;

  if(connectToAccessPoint(false)){
    server.on("/configure", HTTP_GET, handleGetConfigure);
    server.on("/configure", HTTP_POST, handlePostConfigure);

    server.on("/pressure", HTTP_GET, handleGetPressure);
    server.on("/temperature", HTTP_GET, handleGetTemperature);
    server.on("/humidity", HTTP_GET, handleGetHumidity);
    server.on("/distance", HTTP_GET, handleGetDistance);
    server.on("/duration", HTTP_GET, handleGetDuration);

    server.on("/trigger/report", HTTP_POST, handleTriggerReport);
    server.on("/all/aggregated", HTTP_GET, handleGetAllAggregated);

    server.on("/all/actual", HTTP_GET, handleGetAllActual);

    server.onNotFound(handleNotFound);

    server.begin();                  //Start server

    Serial.println("HTTP server started");

  }else{
    ret = false;
    Serial.println("HTTP server did not start because the connection is not OK");
  }

  return ret;
}
